christian-kramer/Overwatch-Reaper-Costume/Reference Images/384cf658570ae1bcbe017ebe22efb558.png

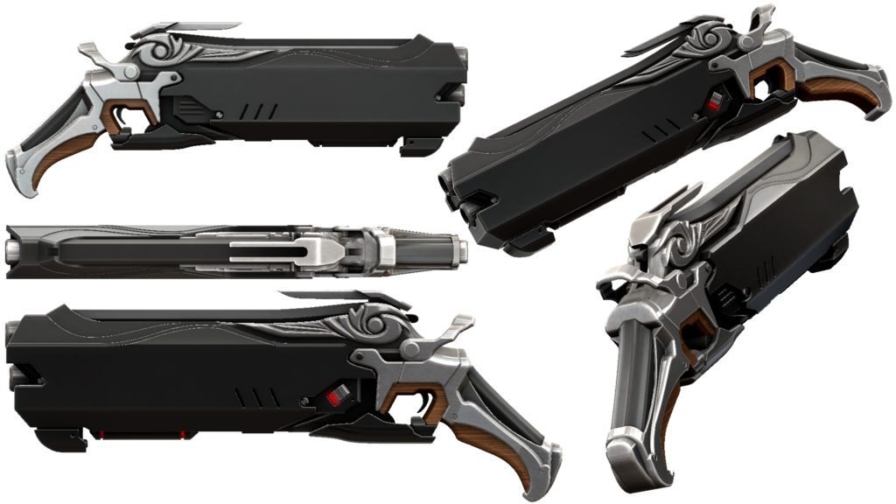
Reference Images/384cf658570ae1bcbe017ebe22efb558.png
