christian-kramer/Overwatch-Reaper-Costume/Reference Images/Reaper_Enigmatic.jpg

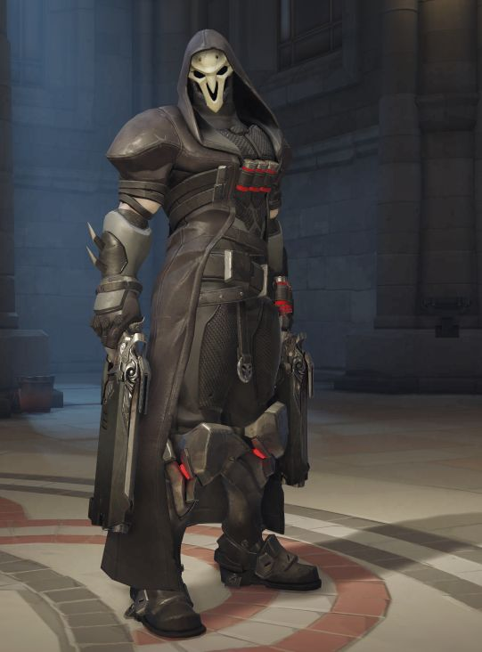
Reference Images/Reaper_Enigmatic.jpg
