christian-kramer/Overwatch-Reaper-Costume/Mechanical/Armor/To Print/Left Calf Cover Top Parts/Left Calf Cover Top Part 8.stl

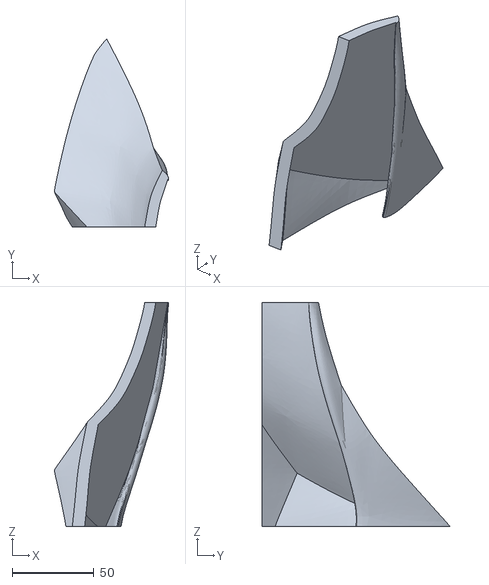
[picture p23: CAD file, 2019-10-07]
Mechanical/Armor/To Print/Left Calf Cover Top Parts/Left Calf Cover Top Part 8.stl
70.2 x 115.3 x 137.3
