christian-kramer/Overwatch-Reaper-Costume/Mechanical/Armor/To Print/Right Kneecap.stl

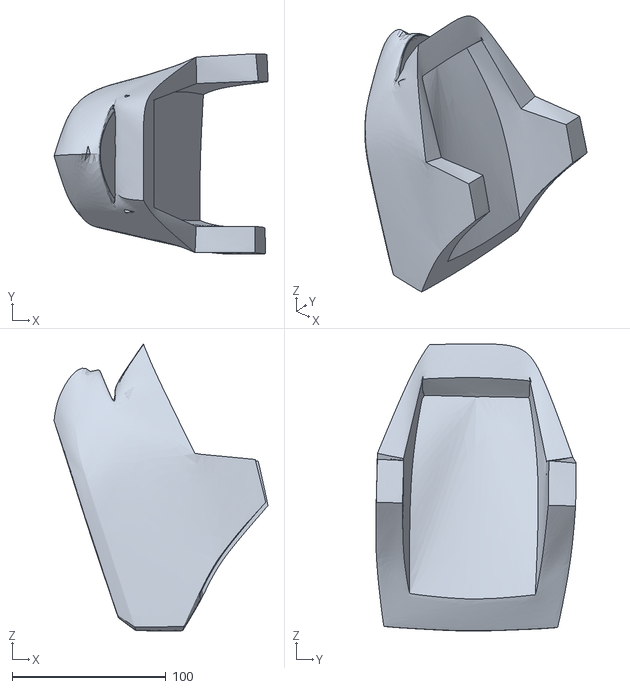
[picture p24: CAD file, 2019-10-07]
Mechanical/Armor/To Print/Right Kneecap.stl
139.2 x 130.5 x 186.8
