christian-kramer/Overwatch-Reaper-Costume/Mechanical/Details/2reaper-emblem.stl

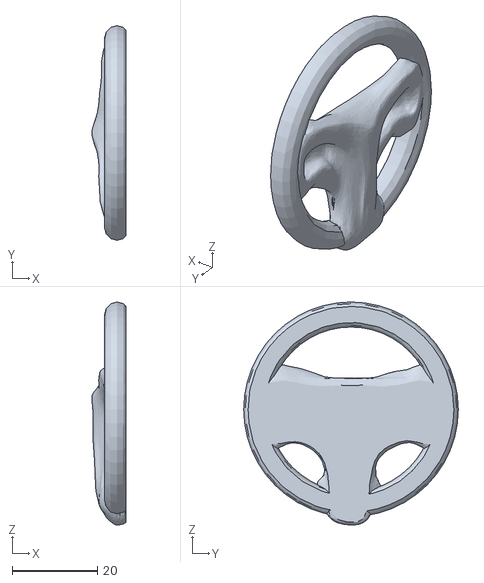
[picture p25: CAD file, 2019-08-23]
Mechanical/Details/2reaper-emblem.stl
8.07 x 50.5 x 52.4
