christian-kramer/Overwatch-Reaper-Costume/Mechanical/Details/To Print/Belt Case Lower Shell.stl

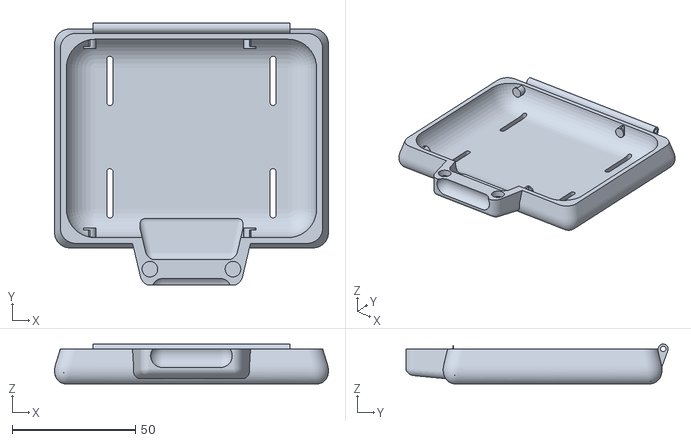
[picture p26: CAD file, 2019-08-24]
Mechanical/Details/To Print/Belt Case Lower Shell.stl
111.1 x 106.4 x 16.2
