christian-kramer/Overwatch-Reaper-Costume/Mechanical/Gun/Original/Hellfire-shot-guns-Brown-hellfire-handle-C.STL

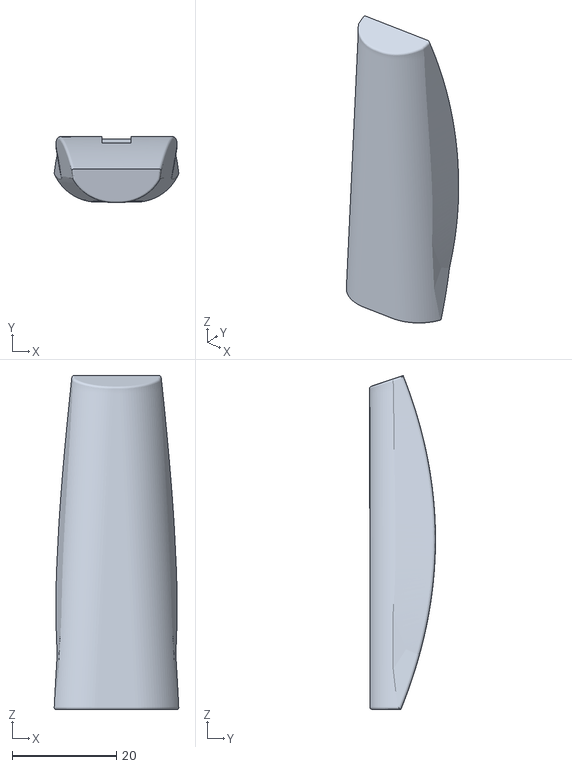
[picture p27: CAD file, 2019-04-04]
Mechanical/Gun/Original/Hellfire-shot-guns-Brown-hellfire-handle-C.STL
23.9 x 12.7 x 64.1
