christian-kramer/Overwatch-Reaper-Costume/Mechanical/Gun/Test/Right Hand Larger.stl

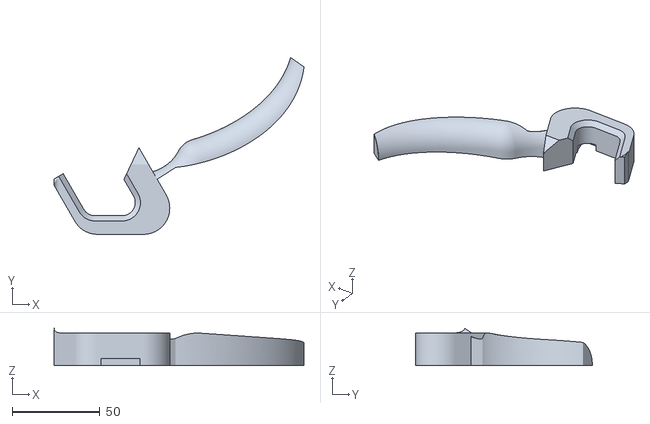
[picture p28: CAD file, 2019-04-12]
Mechanical/Gun/Test/Right Hand Larger.stl
142.7 x 100.9 x 21.3
