christian-kramer/Overwatch-Reaper-Costume/Mechanical/Gun/To Print/Butt.stl

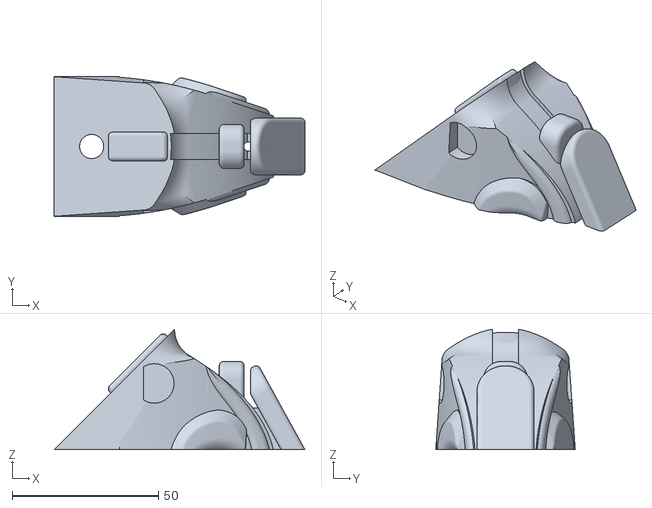
[picture p29: CAD file, 2019-10-12]
Mechanical/Gun/To Print/Butt.stl
85.8 x 47.7 x 41.1
