christian-kramer/Overwatch-Reaper-Costume/Mechanical/PCB Ship Container/To Print/Lid.stl

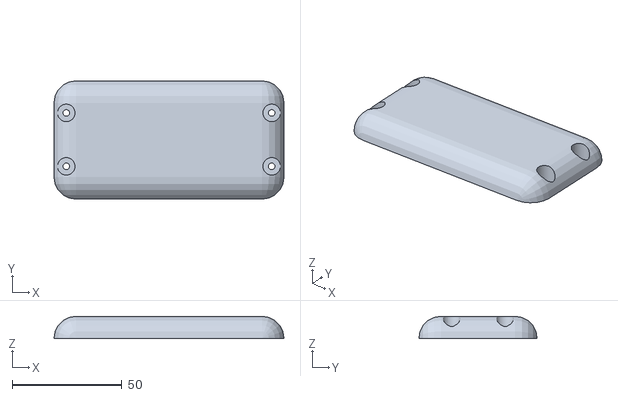
[picture p30: CAD file, 2019-08-11]
Mechanical/PCB Ship Container/To Print/Lid.stl
105.0 x 54.0 x 10.2
