christian-kramer/Overwatch-Reaper-Costume/Mechanical/Armor/To Print/Left Calf Cover Top Parts/Left Calf Cover Top Part 6.stl

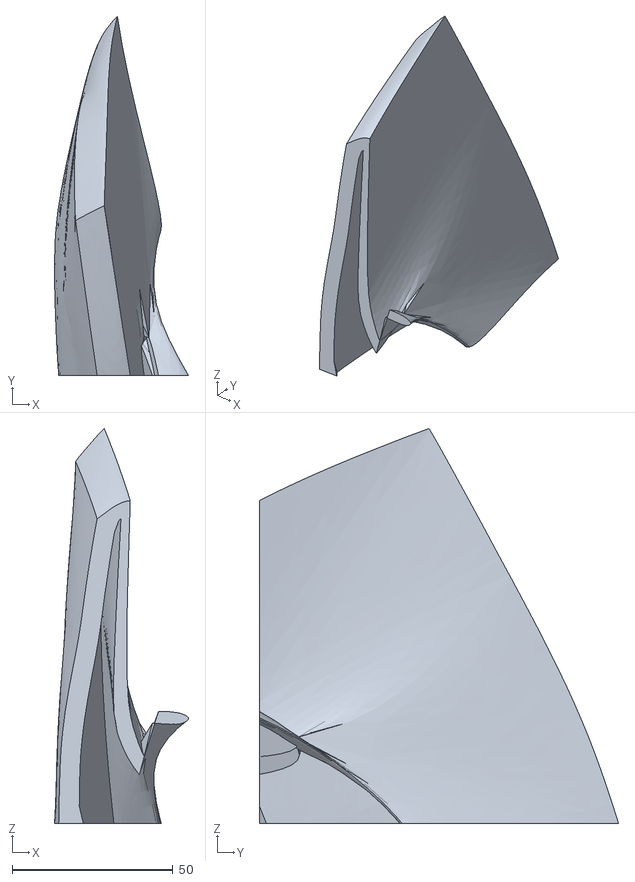
[picture p31: CAD file, 2019-10-07]
Mechanical/Armor/To Print/Left Calf Cover Top Parts/Left Calf Cover Top Part 6.stl
41.6 x 111.6 x 122.7
