christian-kramer/Overwatch-Reaper-Costume/Mechanical/Gun/Components/LED 5mm.STL

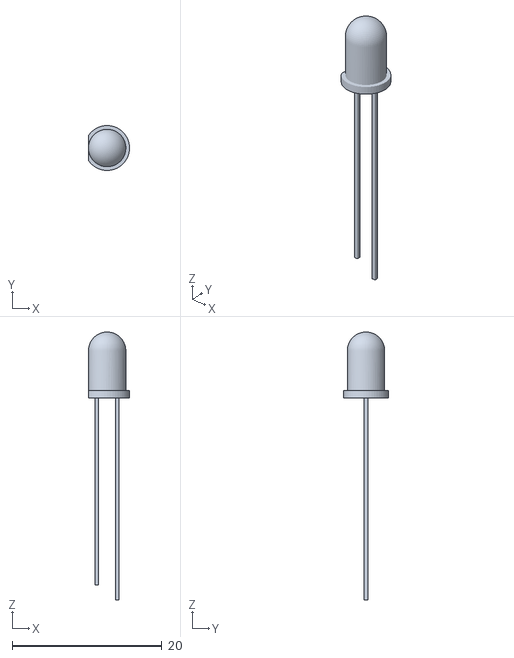
[picture p32: CAD file, 2019-04-12]
Mechanical/Gun/Components/LED 5mm.STL
5.50 x 6.00 x 35.8
