christian-kramer/Overwatch-Reaper-Costume/Mechanical/Gun/Test/Barrel B Top Fixed.stl

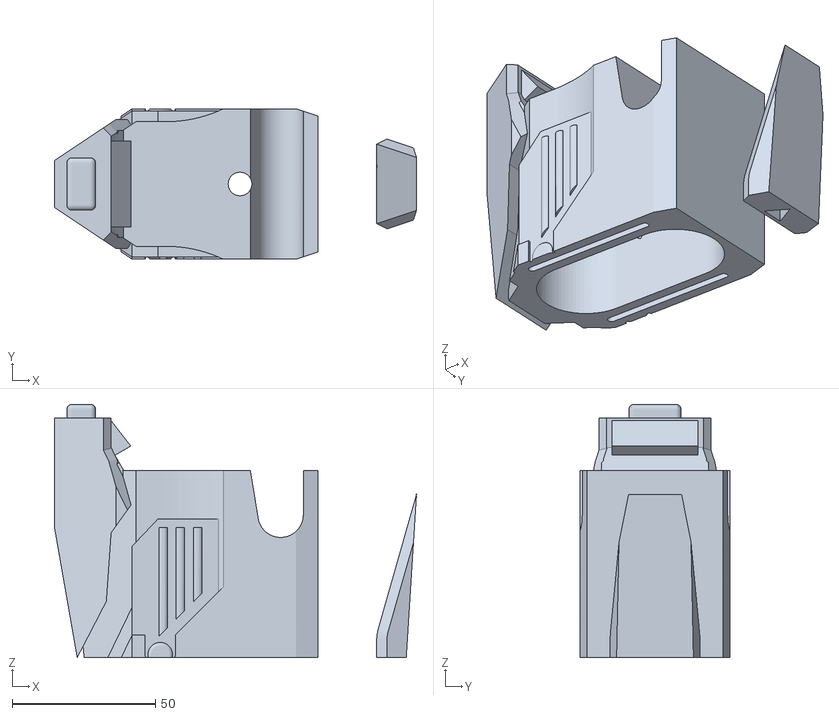
[picture p33: CAD file, 2019-04-12]
Mechanical/Gun/Test/Barrel B Top Fixed.stl
126.3 x 52.5 x 88.3
