christian-kramer/Overwatch-Reaper-Costume/Mechanical/Gun/To Print/Trigger Handles.stl

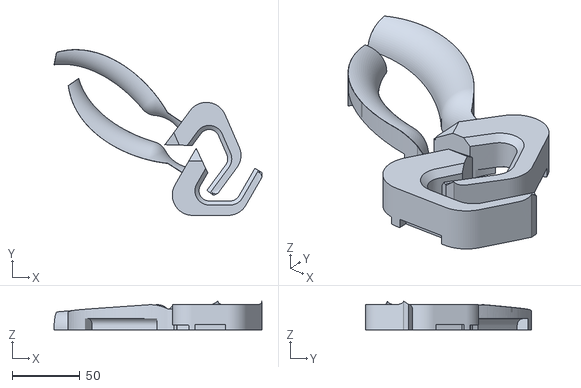
[picture p34: CAD file, 2019-10-12]
Mechanical/Gun/To Print/Trigger Handles.stl
153.2 x 122.1 x 21.2
