christian-kramer/Overwatch-Reaper-Costume/Mechanical/Armor/To Print/Left Calf Cover Bottom Half 1.stl

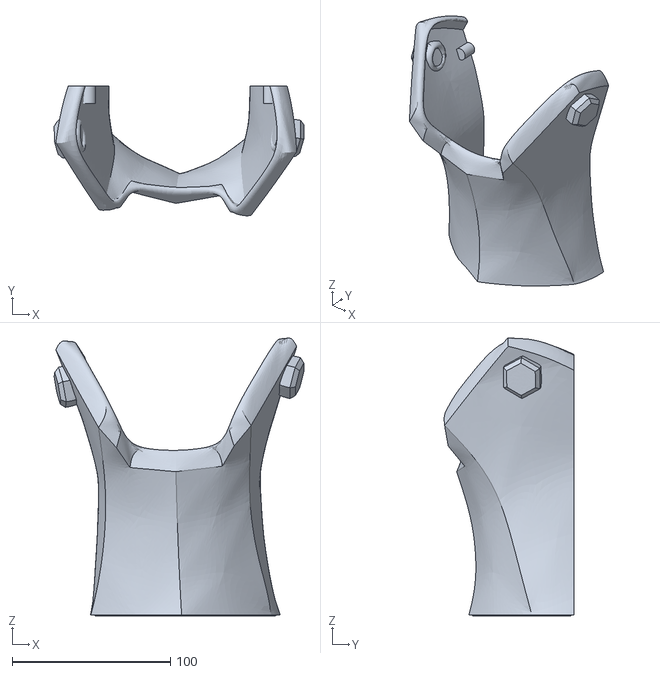
[picture p35: CAD file, 2019-09-20]
Mechanical/Armor/To Print/Left Calf Cover Bottom Half 1.stl
157.6 x 81.9 x 175.4
