christian-kramer/Overwatch-Reaper-Costume/Mechanical/Armor/To Print/Left Calf Cover Top Parts/Left Calf Cover Top Part 3.stl

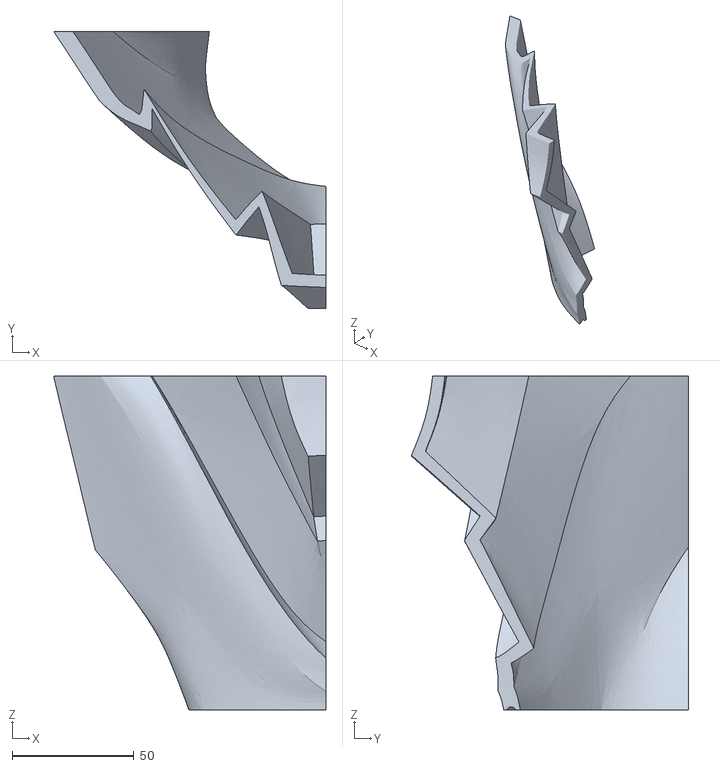
[picture p36: CAD file, 2019-10-07]
Mechanical/Armor/To Print/Left Calf Cover Top Parts/Left Calf Cover Top Part 3.stl
111.7 x 114.0 x 137.3
