christian-kramer/Overwatch-Reaper-Costume/Mechanical/Armor/To Print/Right Calf Cover Top Parts/Right Calf Cover Top Part 4.stl

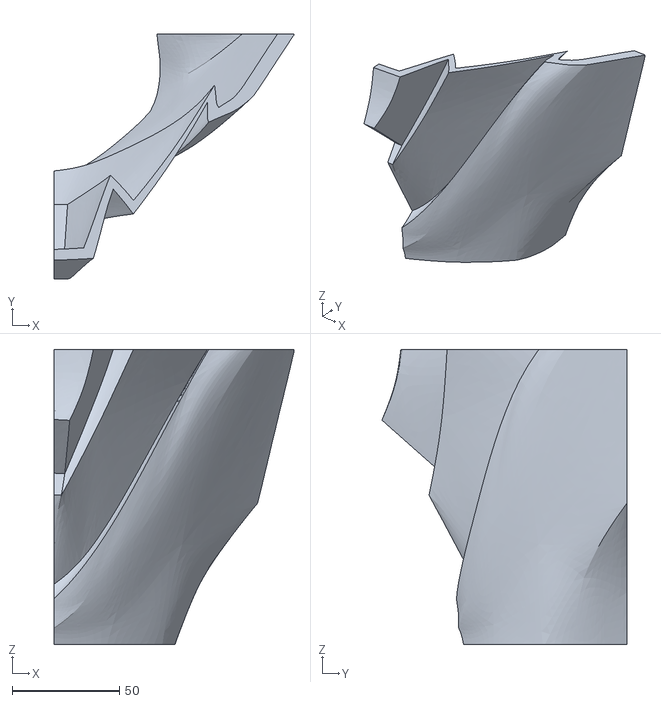
[picture p37: CAD file, 2019-10-07]
Mechanical/Armor/To Print/Right Calf Cover Top Parts/Right Calf Cover Top Part 4.stl
112.1 x 114.4 x 137.8
