christian-kramer/Overwatch-Reaper-Costume/Mechanical/Gun/Components/KEYSTONE 2460.step

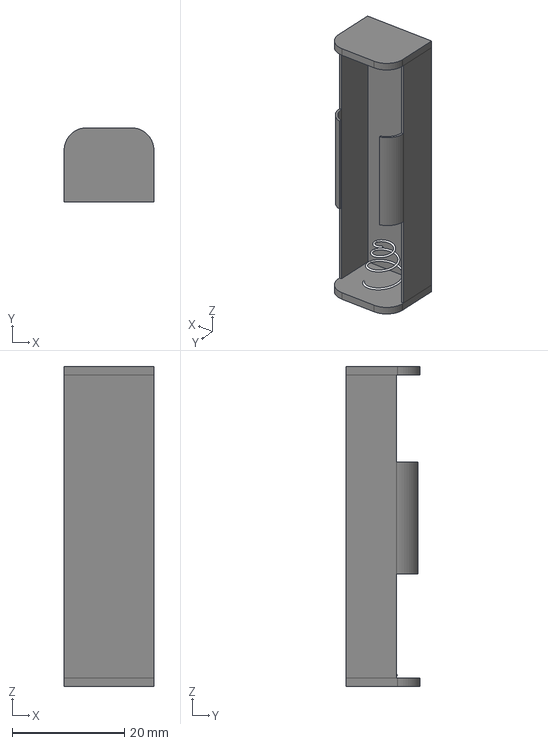
[picture p38: CAD file, 2019-04-12]
Mechanical/Gun/Components/KEYSTONE 2460.step
16.0 x 13.3 x 57.0 mm
