christian-kramer/Overwatch-Reaper-Costume/Mechanical/Gun/Original/Hellfire-shot-guns-Silver-PLA-hellfire-handle.STL

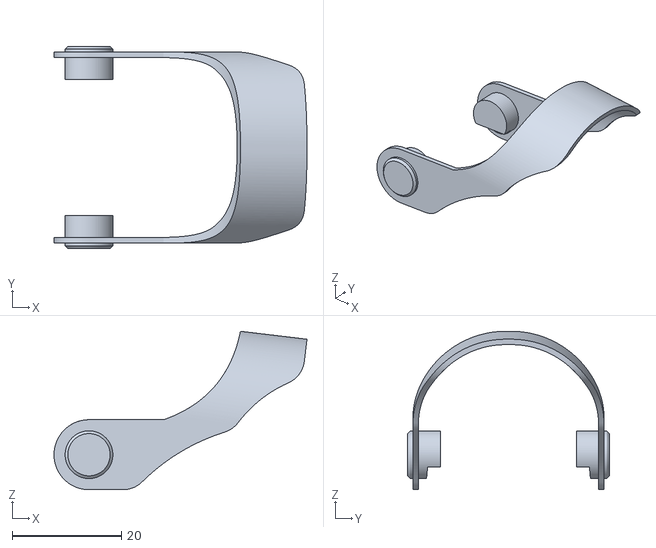
[picture p39: CAD file, 2019-04-04]
Mechanical/Gun/Original/Hellfire-shot-guns-Silver-PLA-hellfire-handle.STL
46.4 x 37.0 x 29.0
