christian-kramer/Overwatch-Reaper-Costume/Mechanical/Gun/Test/Barrel B3.stl

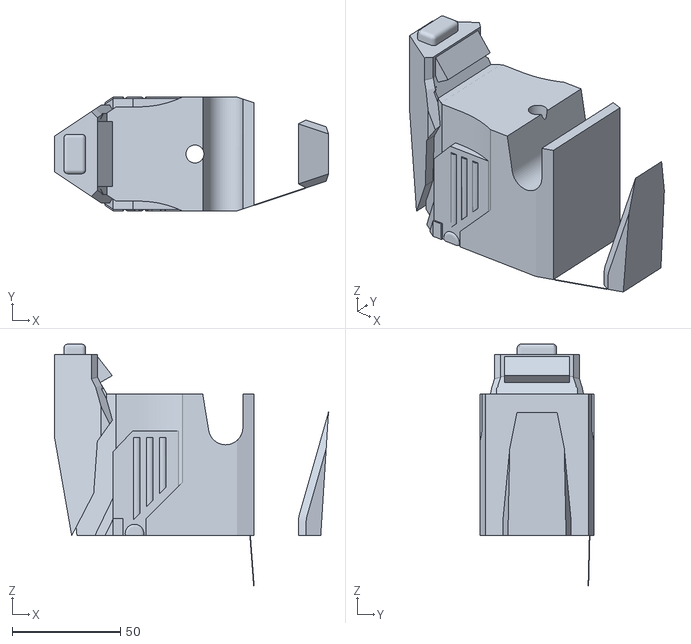
[picture p40: CAD file, 2019-04-12]
Mechanical/Gun/Test/Barrel B3.stl
126.3 x 52.5 x 111.5
