christian-kramer/Overwatch-Reaper-Costume/Mechanical/Gun/To Print/Barrel A Shell 1.stl

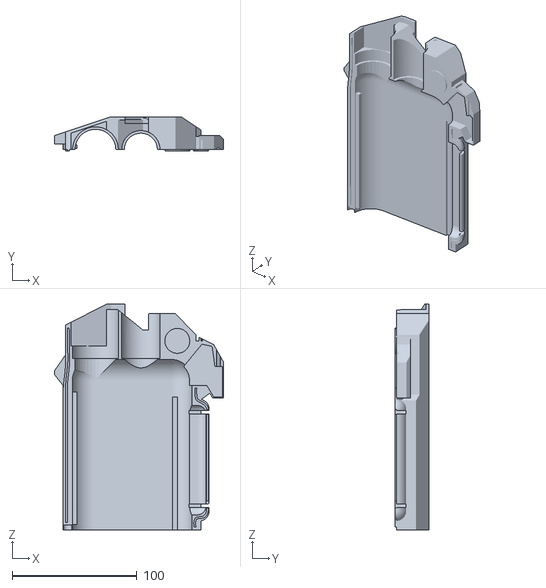
[picture p41: CAD file, 2019-10-12]
Mechanical/Gun/To Print/Barrel A Shell 1.stl
135.9 x 27.3 x 181.5
