christian-kramer/Overwatch-Reaper-Costume/Mechanical/Armor/To Print/Left Calf Cover Top Parts/Left Calf Cover Top Part 5.stl

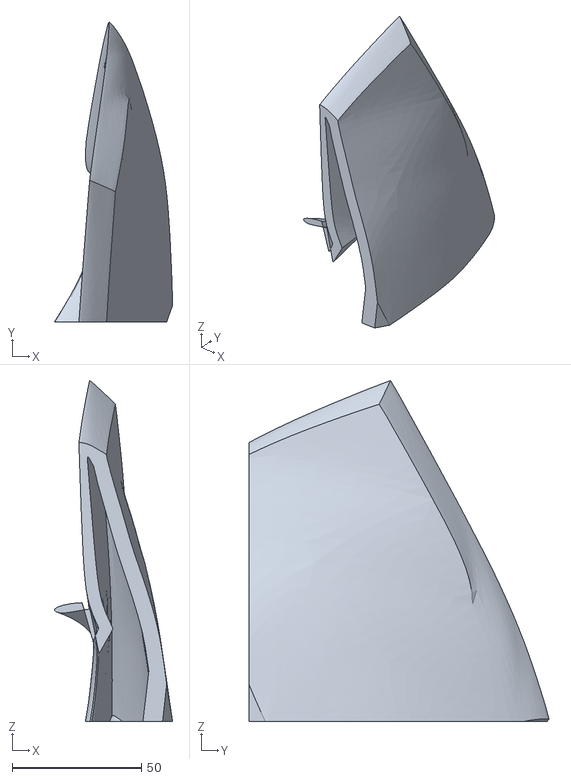
[picture p42: CAD file, 2019-10-07]
Mechanical/Armor/To Print/Left Calf Cover Top Parts/Left Calf Cover Top Part 5.stl
45.7 x 116.1 x 131.9
