christian-kramer/Overwatch-Reaper-Costume/Mechanical/Armor/To Print/Right Calf Cover Top Parts/Right Calf Cover Top Part 3.stl

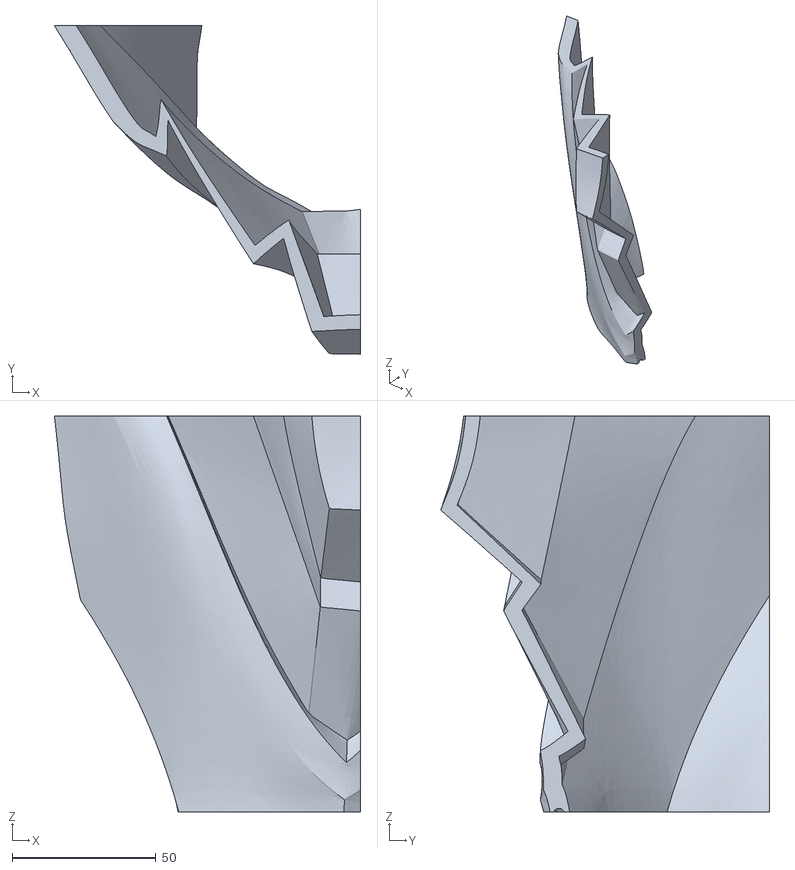
[picture p43: CAD file, 2019-10-07]
Mechanical/Armor/To Print/Right Calf Cover Top Parts/Right Calf Cover Top Part 3.stl
106.5 x 114.3 x 137.8
