christian-kramer/Overwatch-Reaper-Costume/Mechanical/Gun/Original/Hellfire-shot-guns-Silver-PLA-hellfire-barrel.STL

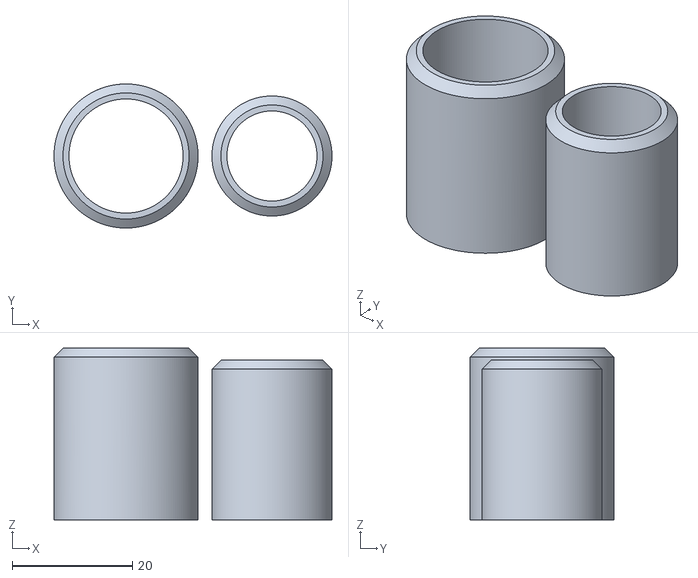
[picture p44: CAD file, 2019-04-04]
Mechanical/Gun/Original/Hellfire-shot-guns-Silver-PLA-hellfire-barrel.STL
46.3 x 24.0 x 28.6
