christian-kramer/Overwatch-Reaper-Costume/Mechanical/Gun/Test/Barrel B Bottom.stl

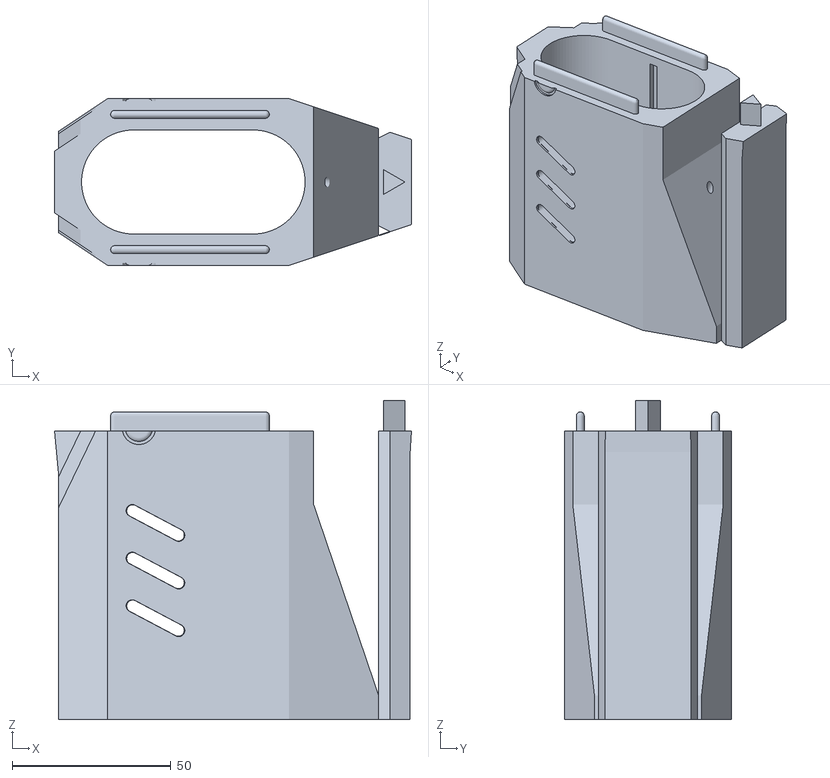
[picture p45: CAD file, 2019-04-12]
Mechanical/Gun/Test/Barrel B Bottom.stl
112.4 x 52.5 x 100.5
