christian-kramer/Overwatch-Reaper-Costume/Mechanical/Gun/To Print/Barrel B Bottom.stl

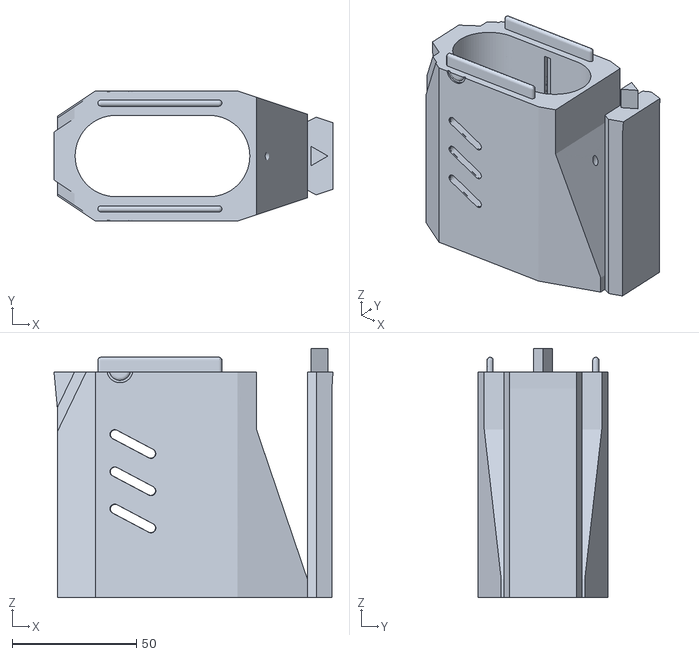
[picture p46: CAD file, 2019-10-12]
Mechanical/Gun/To Print/Barrel B Bottom.stl
112.4 x 52.5 x 100.5
