christian-kramer/Overwatch-Reaper-Costume/Mechanical/Armor/To Print/Left Calf Cover Bottom Half 2.stl

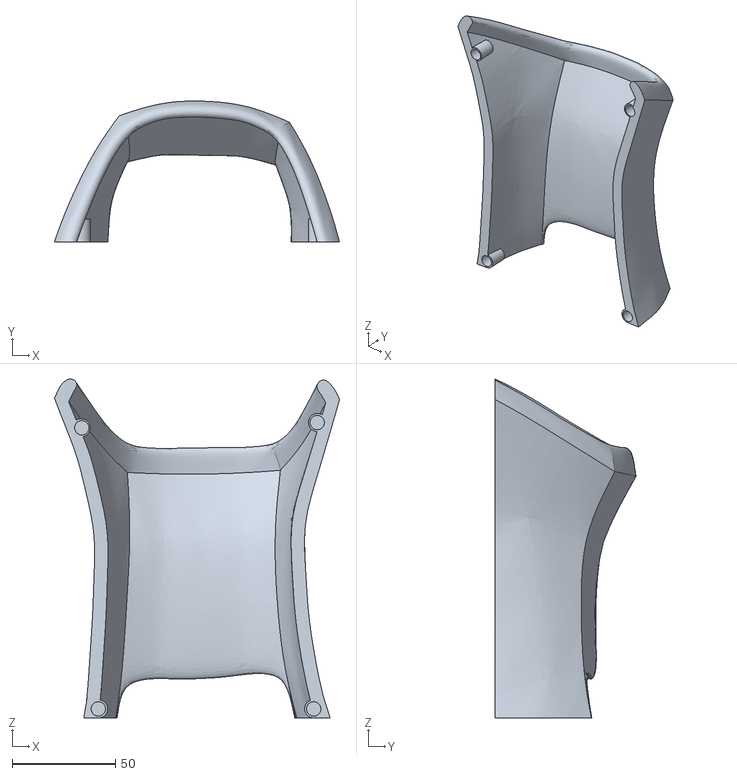
[picture p47: CAD file, 2019-09-20]
Mechanical/Armor/To Print/Left Calf Cover Bottom Half 2.stl
138.2 x 68.3 x 164.4
