christian-kramer/Overwatch-Reaper-Costume/Mechanical/Armor/To Print/Left Calf Cover Top Parts/Left Calf Cover Top Part 2.stl

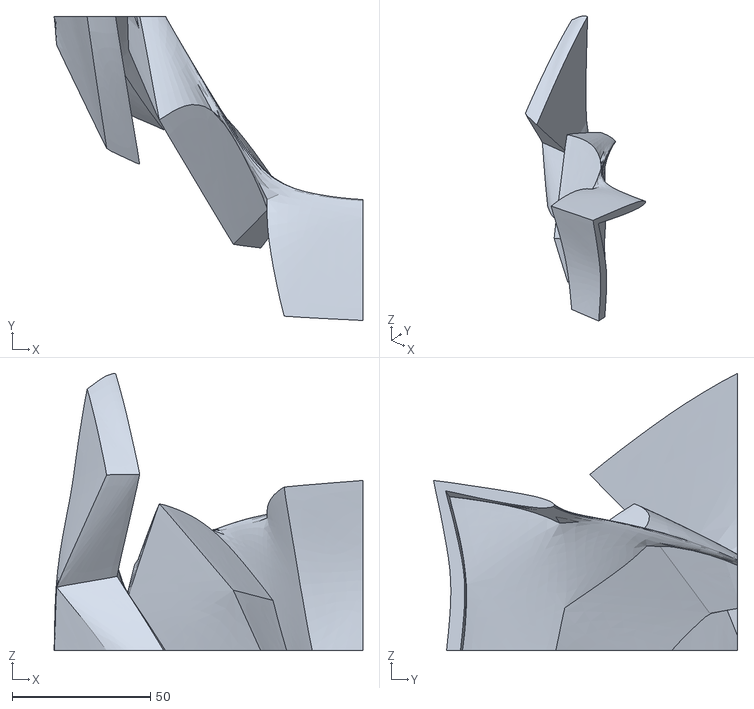
[picture p48: CAD file, 2019-10-07]
Mechanical/Armor/To Print/Left Calf Cover Top Parts/Left Calf Cover Top Part 2.stl
111.7 x 110.0 x 100.3
