christian-kramer/Overwatch-Reaper-Costume/Mechanical/Gun/Test/Barrel B Top.stl

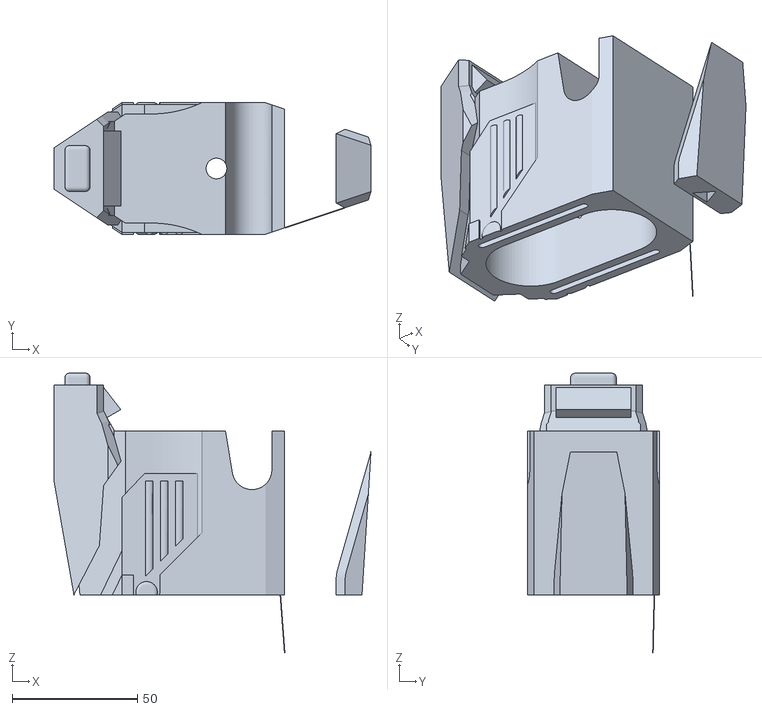
[picture p49: CAD file, 2019-04-12]
Mechanical/Gun/Test/Barrel B Top.stl
126.3 x 52.5 x 111.5
