christian-kramer/Overwatch-Reaper-Costume/Mechanical/Gun/To Print/Trigger Handle Left.stl

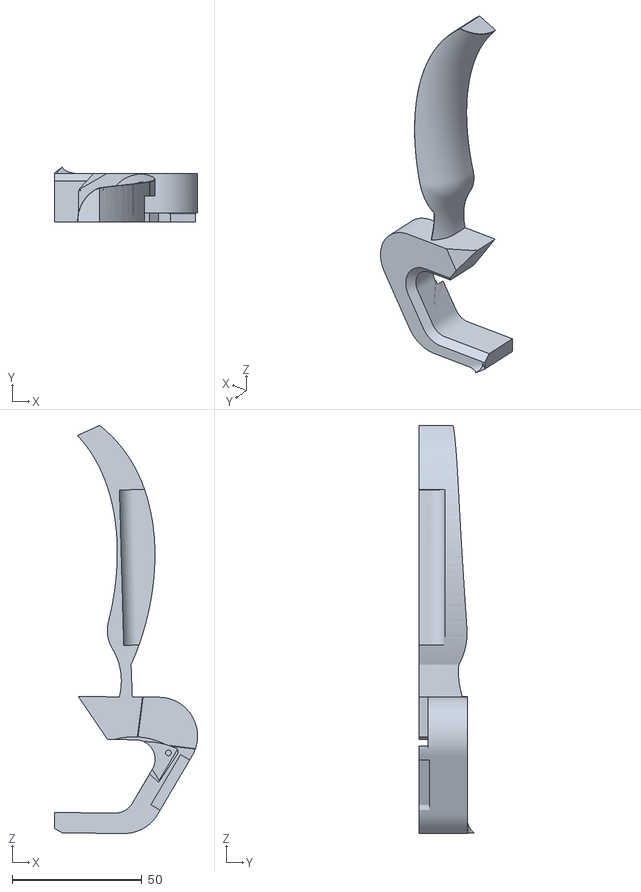
[picture p50: CAD file, 2019-09-25]
Mechanical/Gun/To Print/Trigger Handle Left.stl
55.3 x 21.3 x 157.5
