christian-kramer/Overwatch-Reaper-Costume/Mechanical/Armor/To Print/Right Calf Cover Top Parts/Right Calf Cover Top Part 2.stl

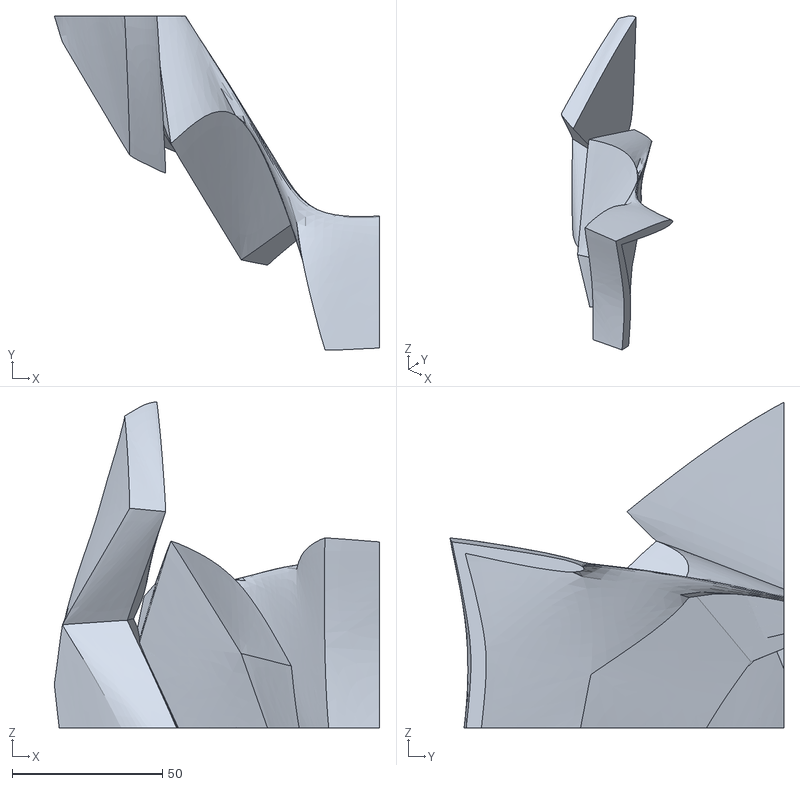
[picture p51: CAD file, 2019-10-07]
Mechanical/Armor/To Print/Right Calf Cover Top Parts/Right Calf Cover Top Part 2.stl
108.2 x 111.0 x 108.2
