christian-kramer/Overwatch-Reaper-Costume/Mechanical/Gun/Original/Hellfire-shot-guns-Silver-PLA-hellfire-back-body-b.STL

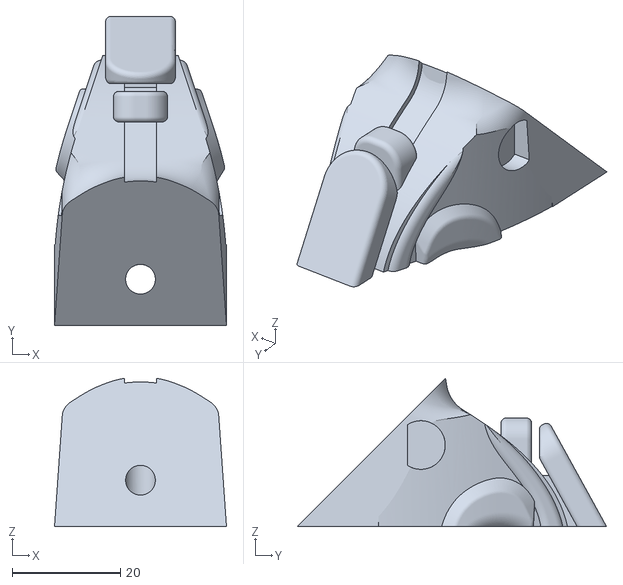
[picture p52: CAD file, 2019-04-04]
Mechanical/Gun/Original/Hellfire-shot-guns-Silver-PLA-hellfire-back-body-b.STL
31.8 x 57.2 x 27.4
