christian-kramer/Overwatch-Reaper-Costume/Mechanical/Gun/Test/hollow.stl

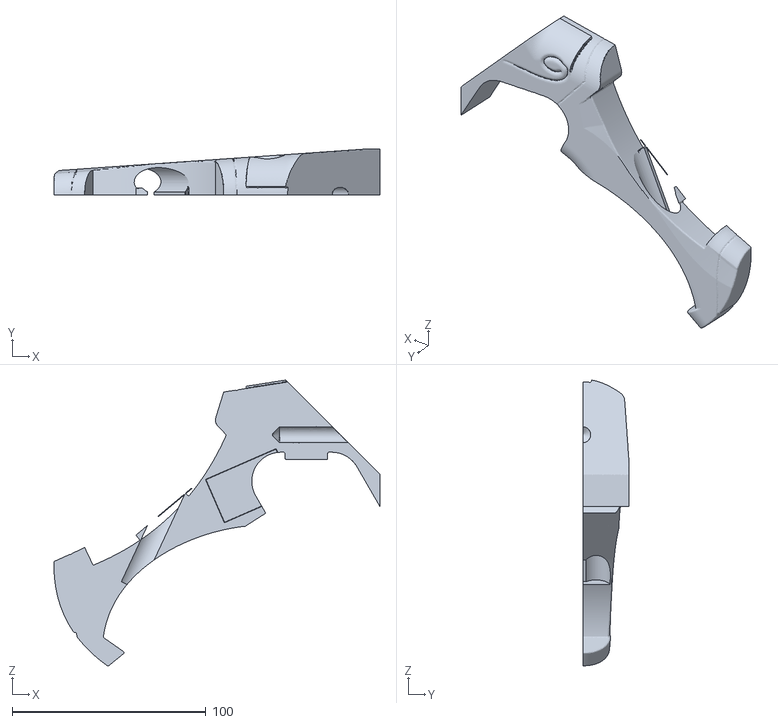
[picture p53: CAD file, 2019-04-12]
Mechanical/Gun/Test/hollow.stl
168.3 x 24.0 x 147.5
