christian-kramer/Overwatch-Reaper-Costume/Mechanical/Armor/To Print/Left Calf Cover Top.stl

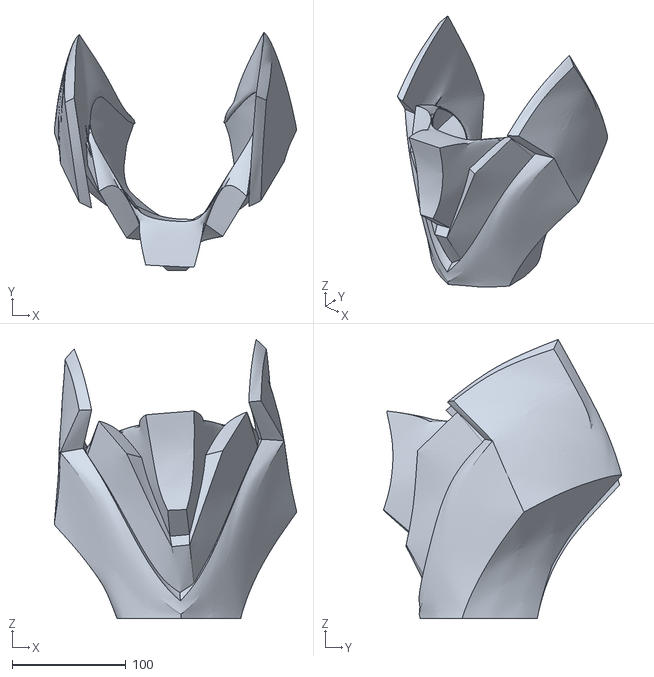
[picture p54: CAD file, 2019-09-18]
Mechanical/Armor/To Print/Left Calf Cover Top.stl
213.0 x 209.4 x 245.0
