christian-kramer/Overwatch-Reaper-Costume/Mechanical/Gun/Original/Hellfire-shot-guns-Black-PLA-hellfire-trigger.STL

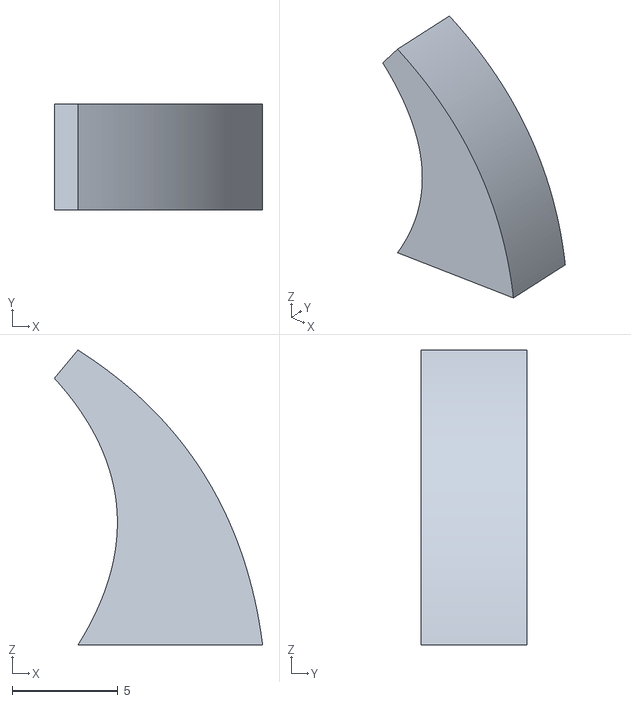
[picture p55: CAD file, 2019-04-04]
Mechanical/Gun/Original/Hellfire-shot-guns-Black-PLA-hellfire-trigger.STL
9.85 x 5.00 x 13.9
