christian-kramer/Overwatch-Reaper-Costume/Mechanical/Gun/To Print/Speaker Tray.stl

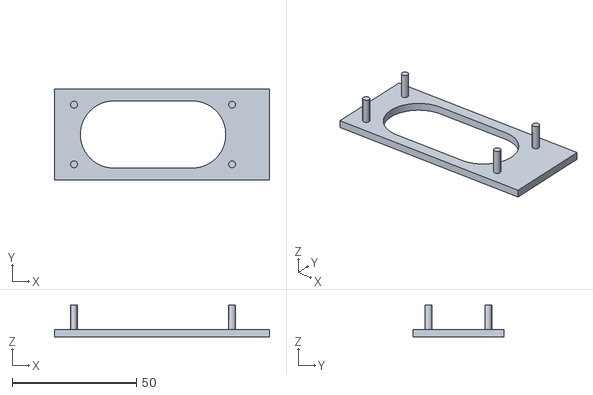
[picture p56: CAD file, 2019-09-24]
Mechanical/Gun/To Print/Speaker Tray.stl
86.5 x 36.7 x 12.7
