christian-kramer/Overwatch-Reaper-Costume/Mechanical/Armor/To Print/Boot Heel Decoration.stl

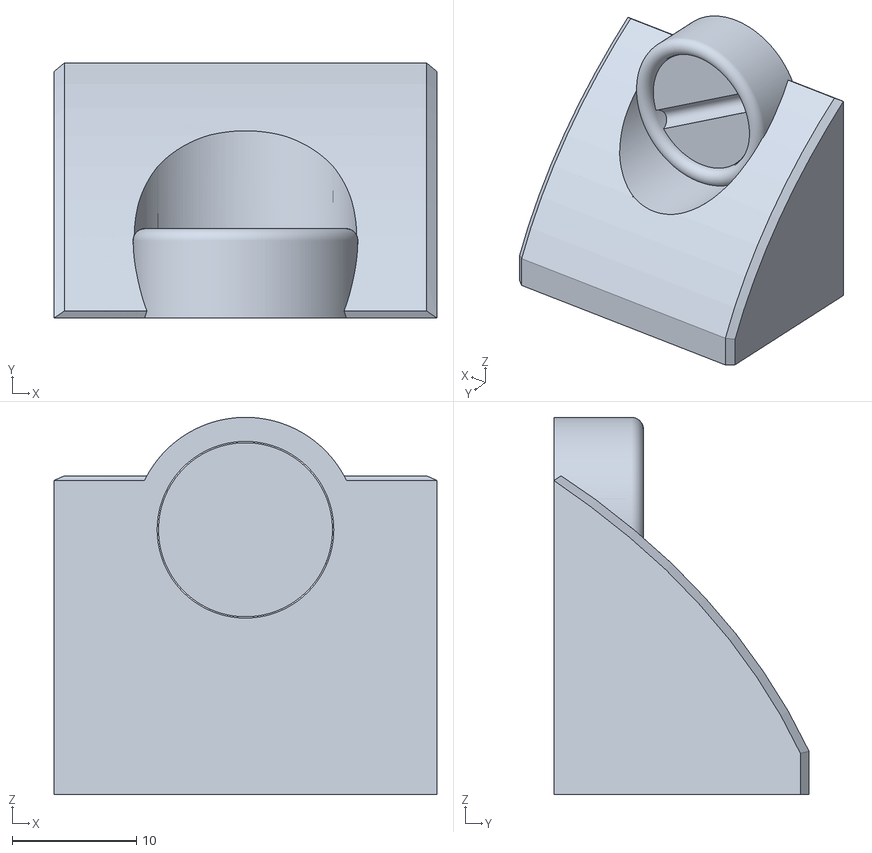
[picture p57: CAD file, 2019-09-12]
Mechanical/Armor/To Print/Boot Heel Decoration.stl
30.9 x 20.6 x 30.4
