christian-kramer/Overwatch-Reaper-Costume/Mechanical/Armor/To Print/Left Hand Spike.stl

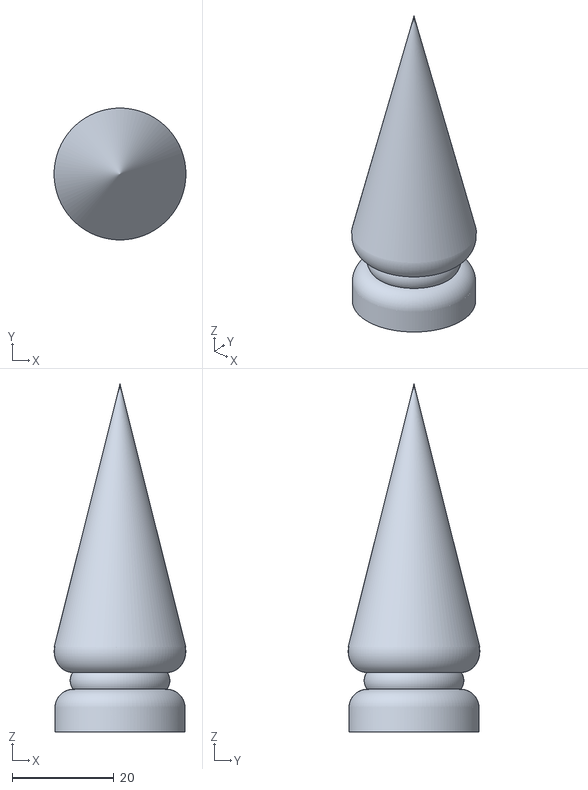
[picture p58: CAD file, 2019-09-12]
Mechanical/Armor/To Print/Left Hand Spike.stl
25.9 x 25.9 x 68.4
