christian-kramer/Overwatch-Reaper-Costume/Mechanical/Gun/To Print/Trigger-Thin.stl

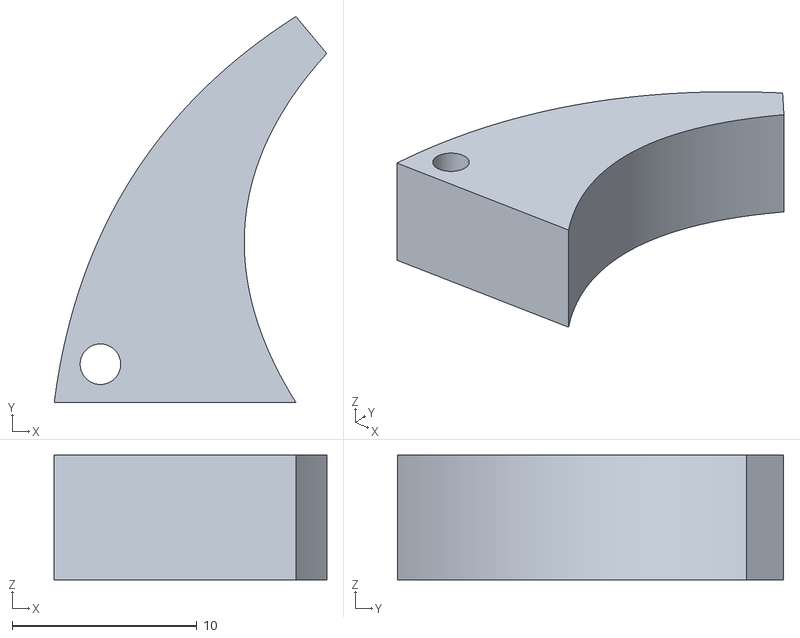
[picture p59: CAD file, 2019-09-24]
Mechanical/Gun/To Print/Trigger-Thin.stl
14.8 x 20.9 x 6.75
