christian-kramer/Overwatch-Reaper-Costume/Mechanical/Armor/To Print/Left Boot Backing.stl

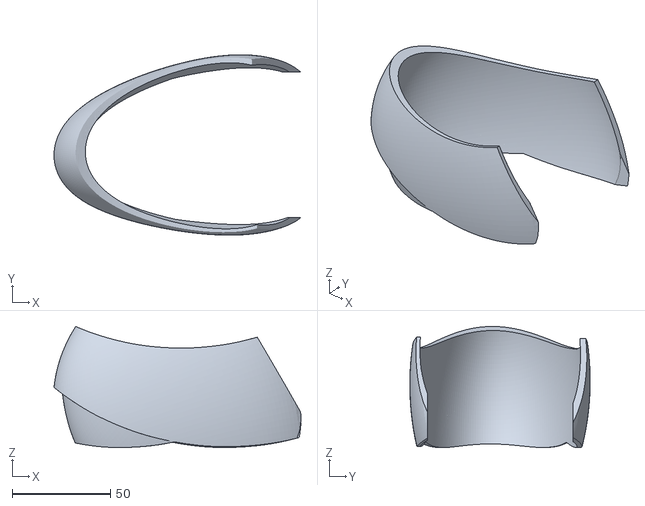
[picture p60: CAD file, 2019-09-11]
Mechanical/Armor/To Print/Left Boot Backing.stl
125.9 x 91.9 x 61.7
