christian-kramer/Overwatch-Reaper-Costume/Mechanical/Gun/To Print/Battery Cover (Wider Cavity).stl

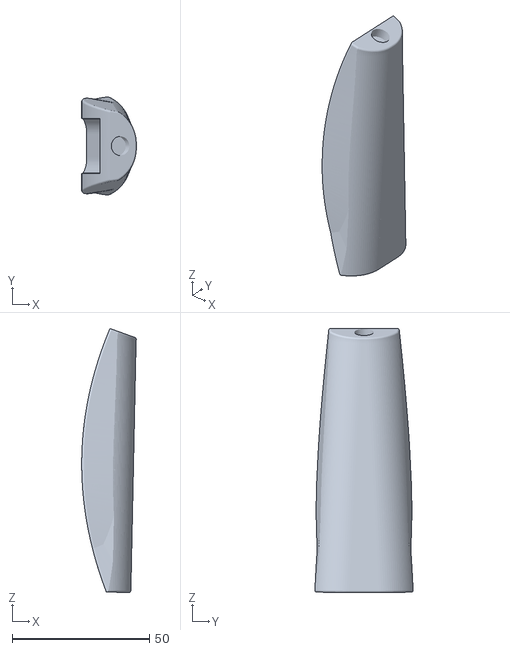
[picture p61: CAD file, 2019-09-24]
Mechanical/Gun/To Print/Battery Cover (Wider Cavity).stl
19.9 x 35.9 x 96.3
