christian-kramer/Overwatch-Reaper-Costume/Mechanical/Armor/To Print/Right Boot Cover.stl

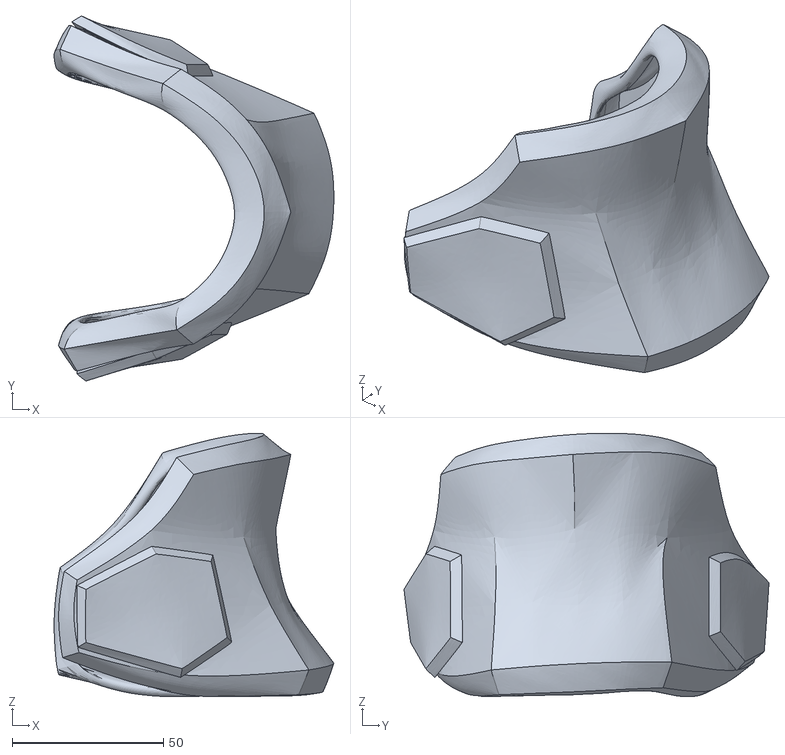
[picture p62: CAD file, 2019-09-11]
Mechanical/Armor/To Print/Right Boot Cover.stl
92.4 x 120.5 x 87.0
