christian-kramer/Overwatch-Reaper-Costume/Mechanical/Gun/To Print/Decorative Barrels.stl

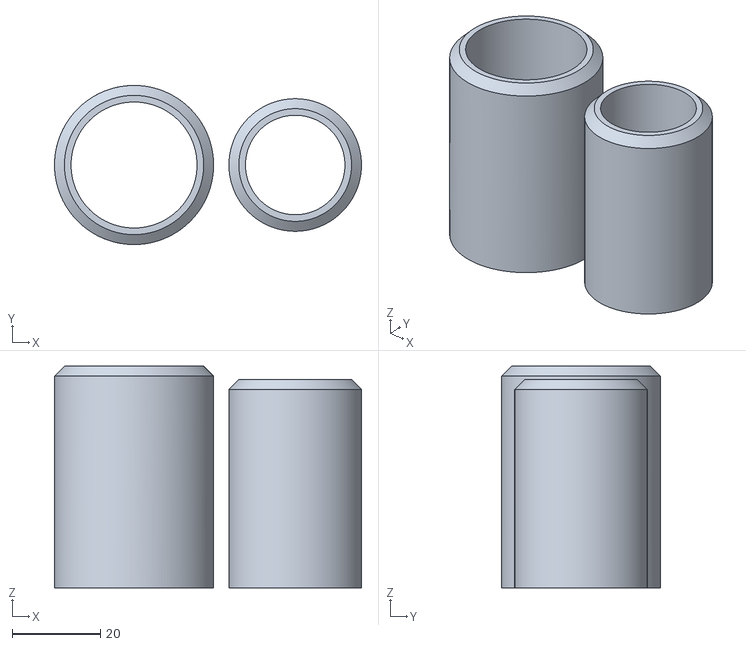
[picture p63: CAD file, 2019-09-14]
Mechanical/Gun/To Print/Decorative Barrels.stl
69.5 x 36.0 x 50.2
