christian-kramer/Overwatch-Reaper-Costume/Mechanical/Armor/To Print/Left Boot Heel.stl

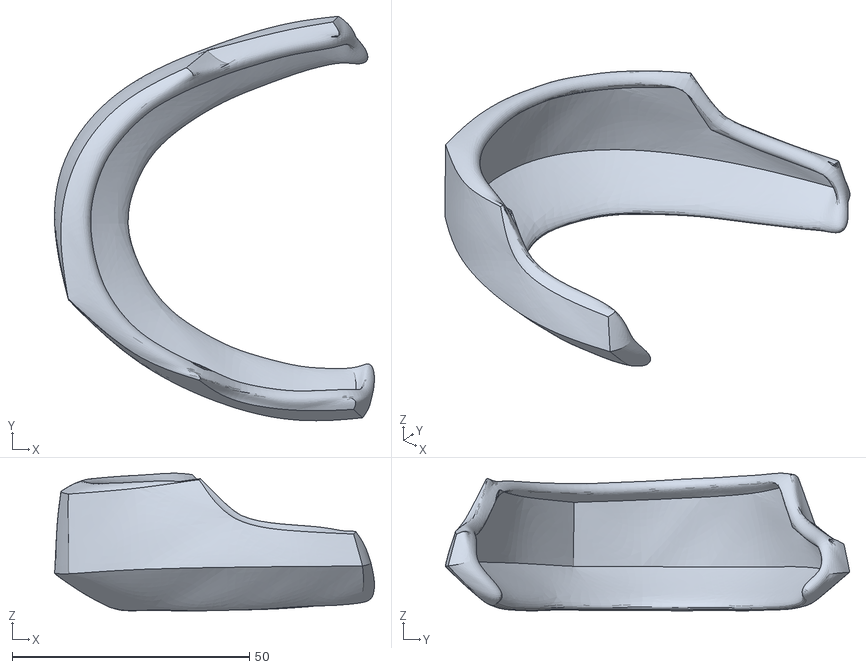
[picture p64: CAD file, 2019-09-11]
Mechanical/Armor/To Print/Left Boot Heel.stl
67.4 x 85.2 x 29.0
