christian-kramer/Overwatch-Reaper-Costume/Mechanical/Gun/To Print/Barrel B Top Decoration.stl

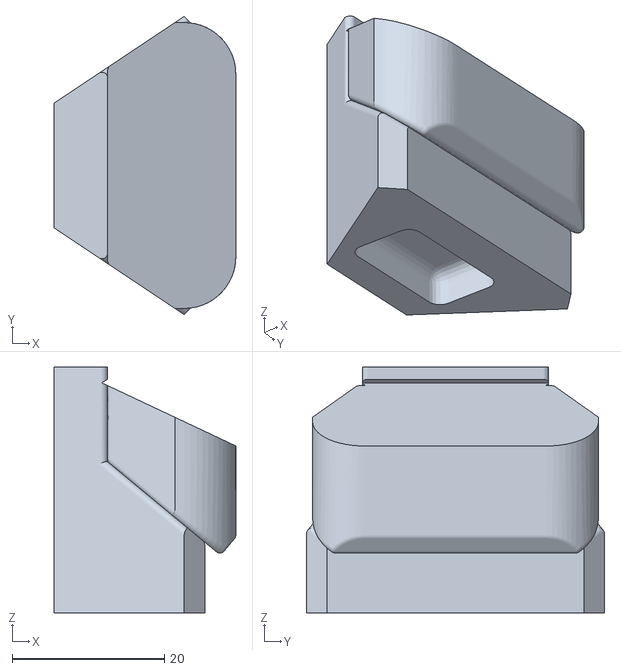
[picture p65: CAD file, 2019-08-12]
Mechanical/Gun/To Print/Barrel B Top Decoration.stl
23.8 x 39.1 x 32.3
