christian-kramer/Overwatch-Reaper-Costume/Mechanical/Gun/To Print/Trigger.stl

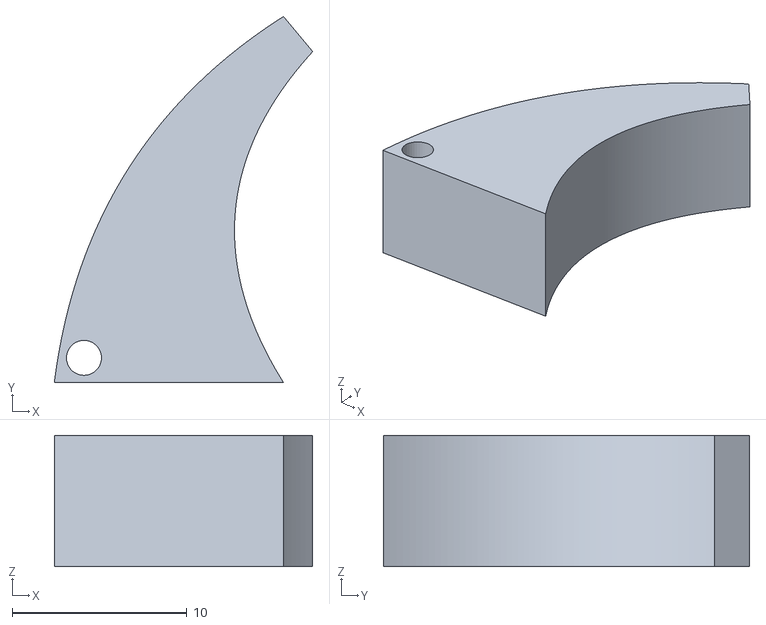
[picture p66: CAD file, 2019-07-21]
Mechanical/Gun/To Print/Trigger.stl
14.8 x 20.9 x 7.50
