christian-kramer/Overwatch-Reaper-Costume/Mechanical/Armor/To Print/Right Hand Cover.stl

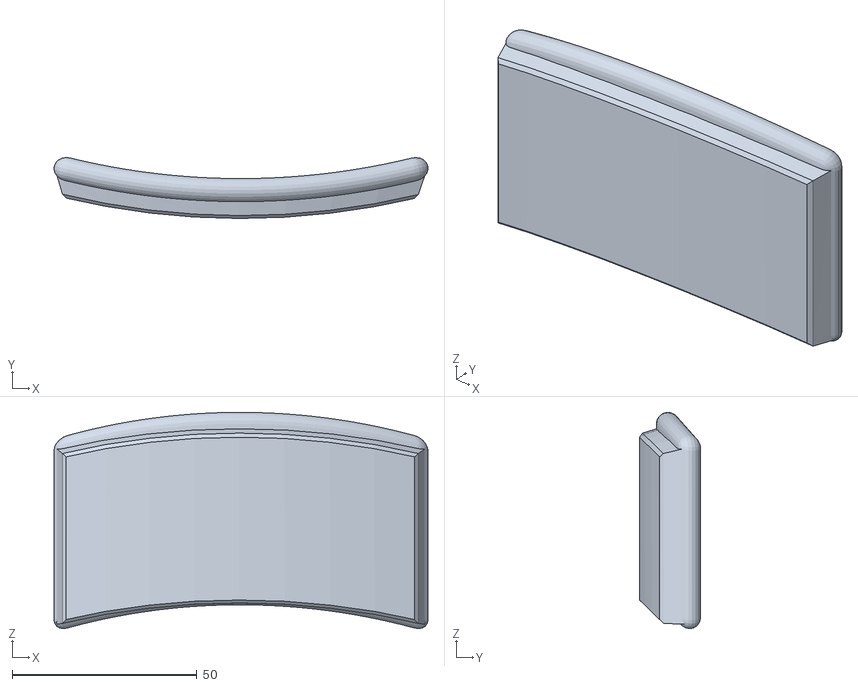
[picture p67: CAD file, 2019-09-05]
Mechanical/Armor/To Print/Right Hand Cover.stl
101.2 x 16.5 x 58.5
