christian-kramer/Overwatch-Reaper-Costume/Mechanical/Gun/To Print/Small Parts.stl

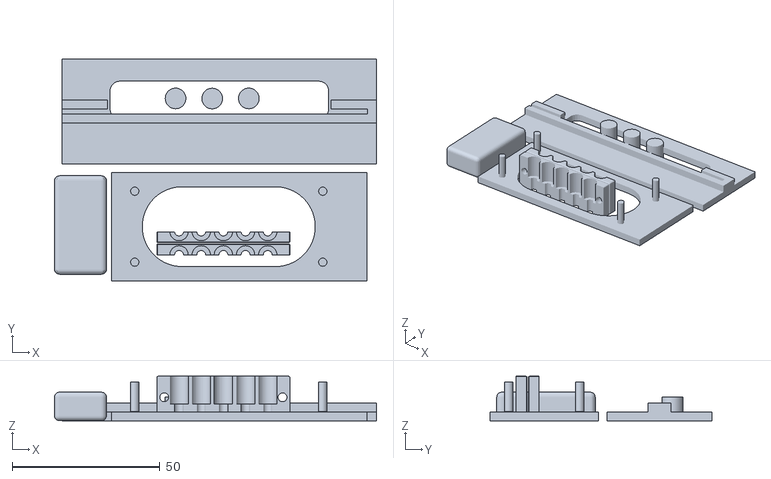
[picture p68: CAD file, 2019-06-20]
Mechanical/Gun/To Print/Small Parts.stl
108.9 x 75.0 x 15.1
