christian-kramer/Overwatch-Reaper-Costume/Mechanical/Armor/To Print/Left Gauntlet Bottom.stl

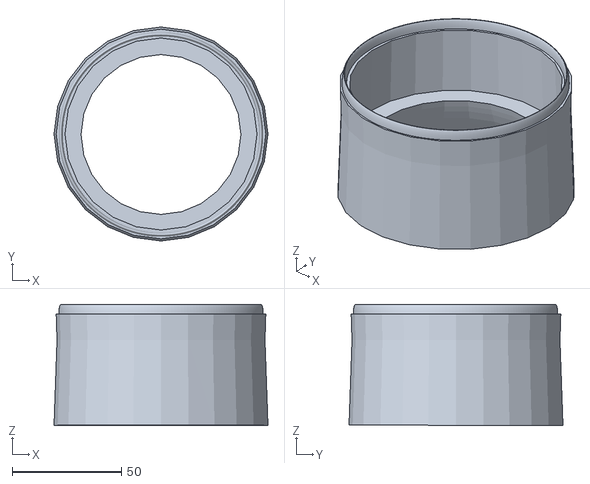
[picture p69: CAD file, 2019-09-04]
Mechanical/Armor/To Print/Left Gauntlet Bottom.stl
98.0 x 98.0 x 55.4
