christian-kramer/Overwatch-Reaper-Costume/Mechanical/Gun/To Print/Decorative Handle.stl

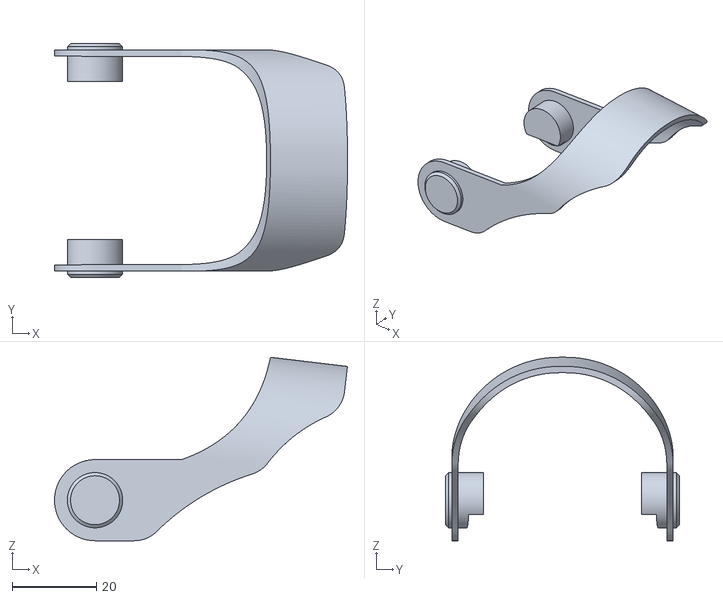
[picture p70: CAD file, 2019-04-12]
Mechanical/Gun/To Print/Decorative Handle.stl
69.5 x 55.5 x 43.5
