christian-kramer/Overwatch-Reaper-Costume/Mechanical/Armor/To Print/Right Gauntlet Shield.stl

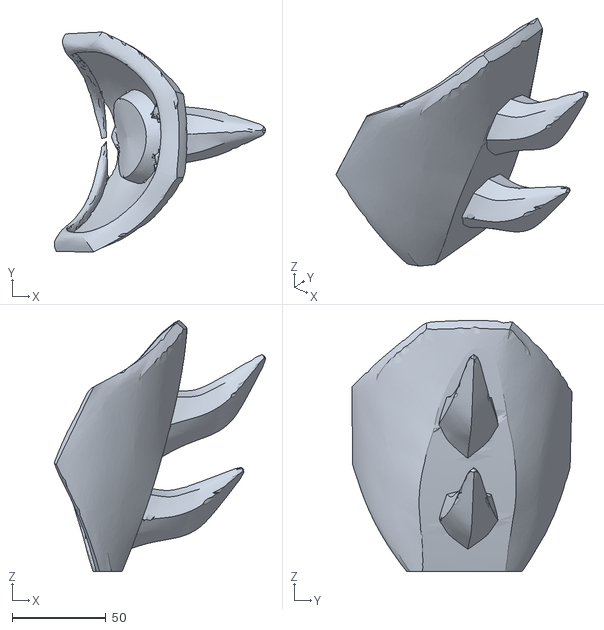
[picture p71: CAD file, 2019-09-04]
Mechanical/Armor/To Print/Right Gauntlet Shield.stl
112.8 x 117.3 x 134.0
