christian-kramer/Overwatch-Reaper-Costume/Mechanical/Gun/To Print/Battery Cover.stl

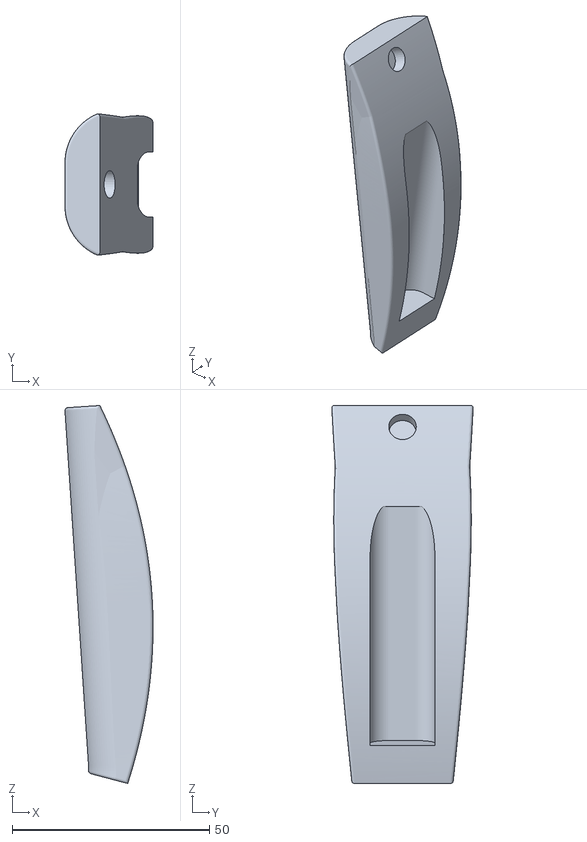
[picture p72: CAD file, 2019-04-12]
Mechanical/Gun/To Print/Battery Cover.stl
22.4 x 35.9 x 95.9
