christian-kramer/Overwatch-Reaper-Costume/Mechanical/Armor/To Print/Right Gauntlet Bottom.stl

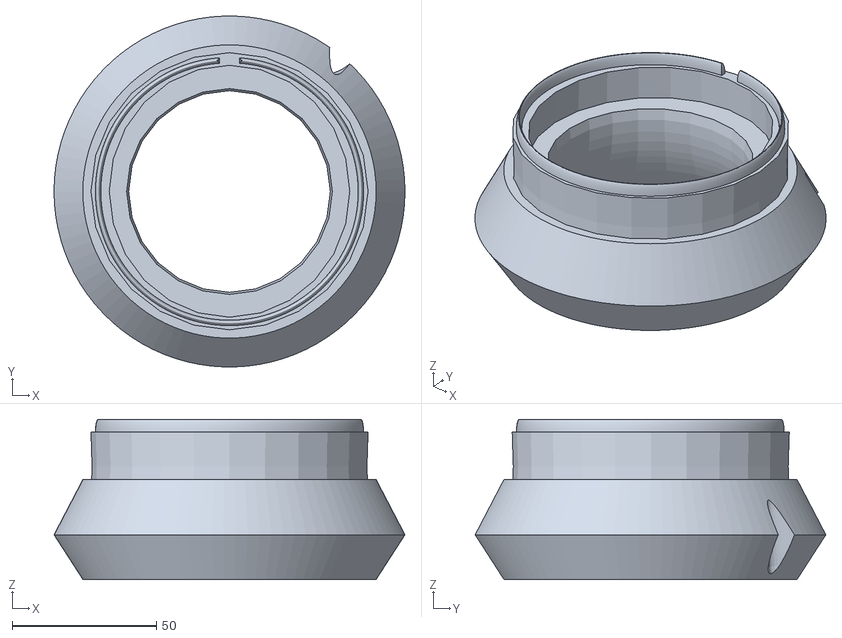
[picture p73: CAD file, 2019-09-04]
Mechanical/Armor/To Print/Right Gauntlet Bottom.stl
121.6 x 121.5 x 55.4
