christian-kramer/Overwatch-Reaper-Costume/Mechanical/Armor/To Print/Right Gauntlet Shield Clean.stl

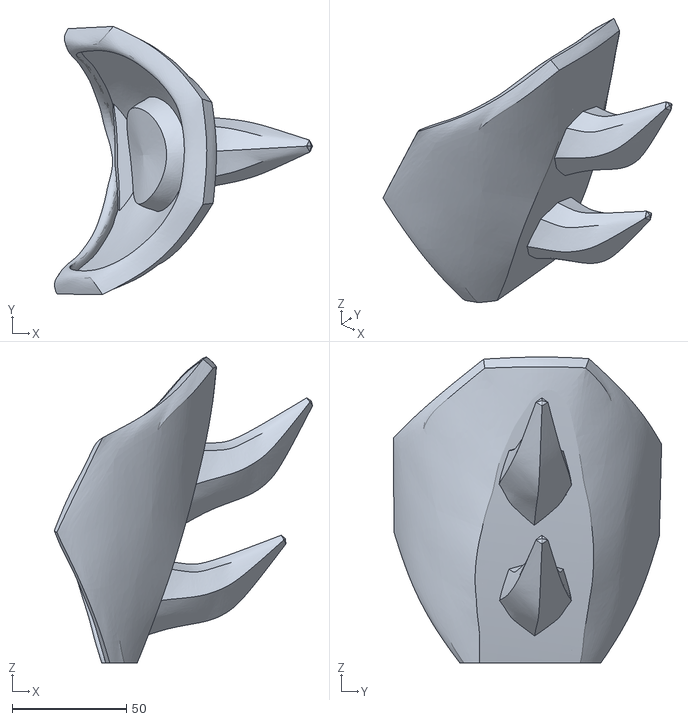
[picture p74: CAD file, 2019-09-04]
Mechanical/Armor/To Print/Right Gauntlet Shield Clean.stl
113.0 x 117.3 x 134.0
