christian-kramer/Overwatch-Reaper-Costume/Mechanical/Armor/To Print/Right Elbow Cover.stl

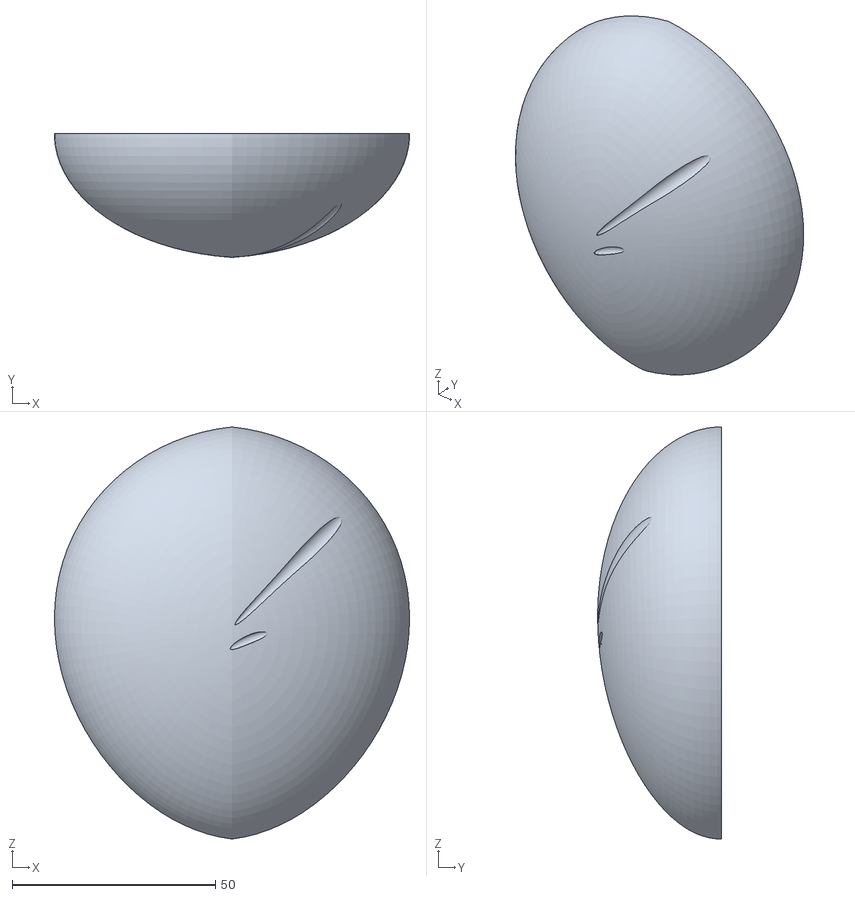
[picture p75: CAD file, 2019-09-04]
Mechanical/Armor/To Print/Right Elbow Cover.stl
87.5 x 30.5 x 101.5
