christian-kramer/Overwatch-Reaper-Costume/Mechanical/Armor/To Print/Right Gauntlet Top.stl

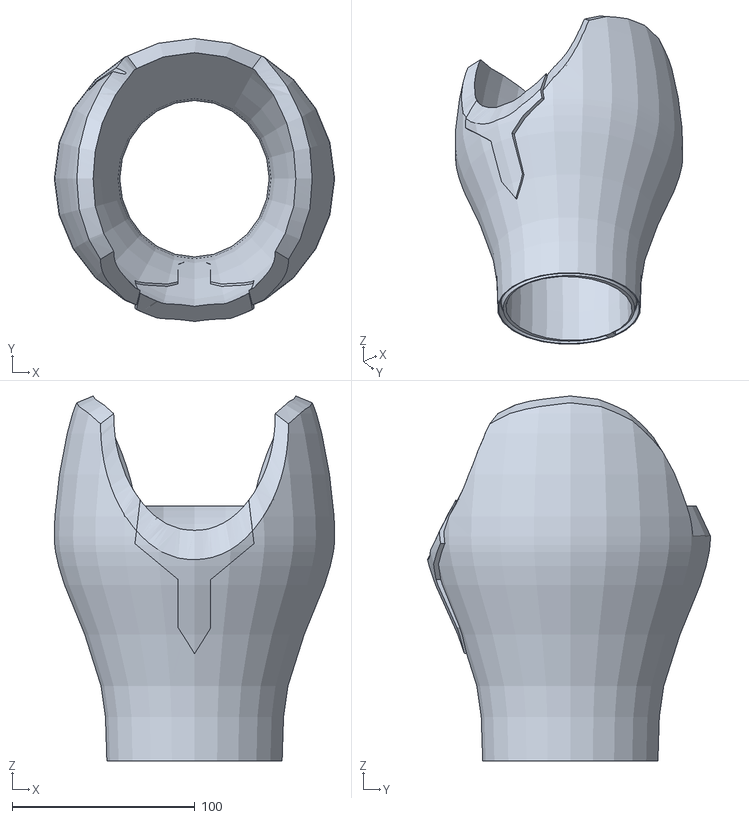
[picture p76: CAD file, 2019-09-04]
Mechanical/Armor/To Print/Right Gauntlet Top.stl
153.6 x 155.0 x 199.9
