christian-kramer/Overwatch-Reaper-Costume/Mechanical/Armor/To Print/Left Gauntlet Shield.stl

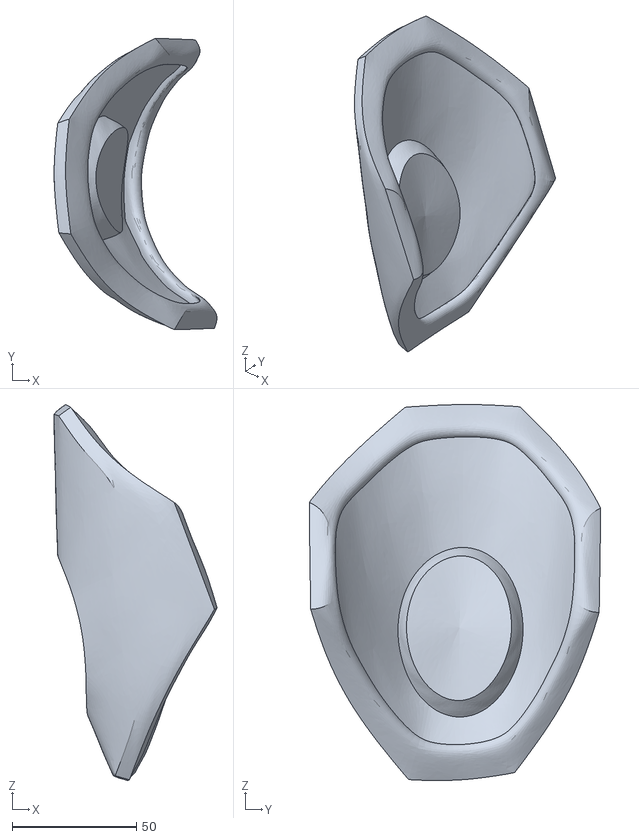
[picture p77: CAD file, 2019-09-04]
Mechanical/Armor/To Print/Left Gauntlet Shield.stl
65.5 x 117.2 x 151.2
