christian-kramer/Overwatch-Reaper-Costume/Mechanical/Armor/To Print/Right Thumb Cover.stl

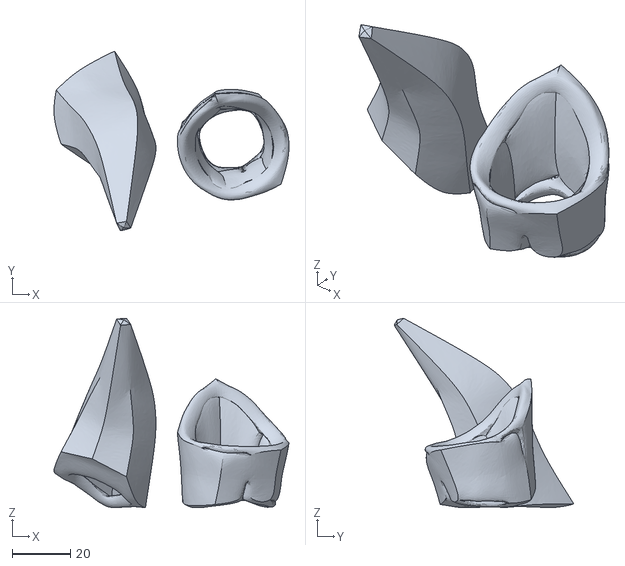
[picture p78: CAD file, 2019-09-03]
Mechanical/Armor/To Print/Right Thumb Cover.stl
80.8 x 61.7 x 65.1
