christian-kramer/Overwatch-Reaper-Costume/Mechanical/Armor/To Print/Right Fingertip Covers.stl

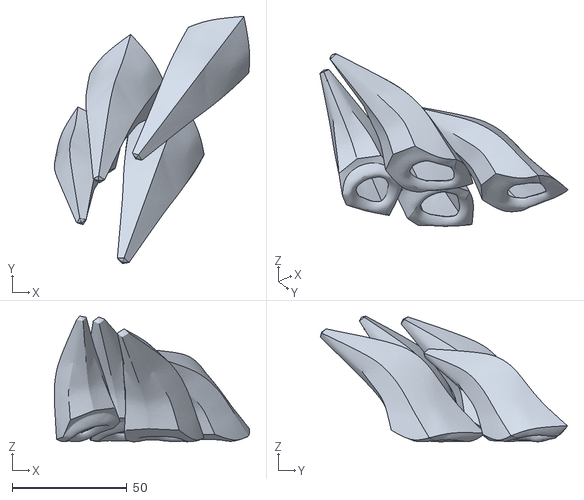
[picture p79: CAD file, 2019-09-03]
Mechanical/Armor/To Print/Right Fingertip Covers.stl
85.0 x 107.5 x 54.7
