christian-kramer/Overwatch-Reaper-Costume/Mechanical/Armor/To Print/Left Fingertip Covers.stl

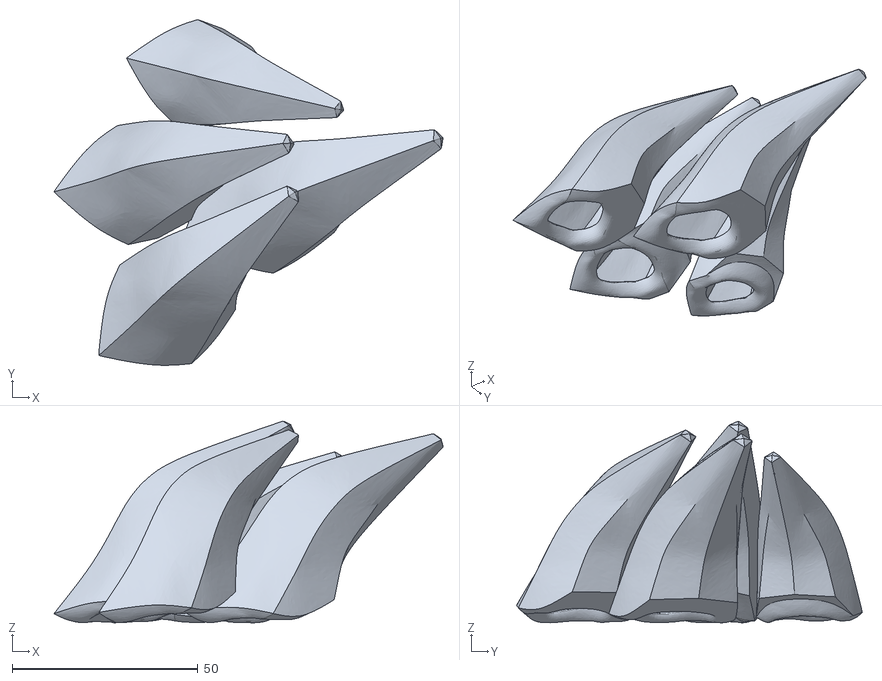
[picture p80: CAD file, 2019-09-03]
Mechanical/Armor/To Print/Left Fingertip Covers.stl
104.7 x 93.1 x 54.3
