christian-kramer/Overwatch-Reaper-Costume/Mechanical/Armor/To Print/Left Thumb Cover.stl

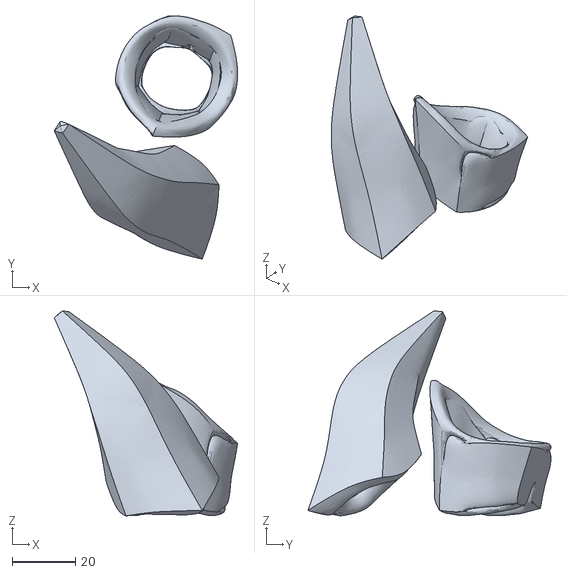
[picture p81: CAD file, 2019-09-02]
Mechanical/Armor/To Print/Left Thumb Cover.stl
57.9 x 76.8 x 64.7
