christian-kramer/Overwatch-Reaper-Costume/Mechanical/Armor/To Print/Left Hand Cover.stl

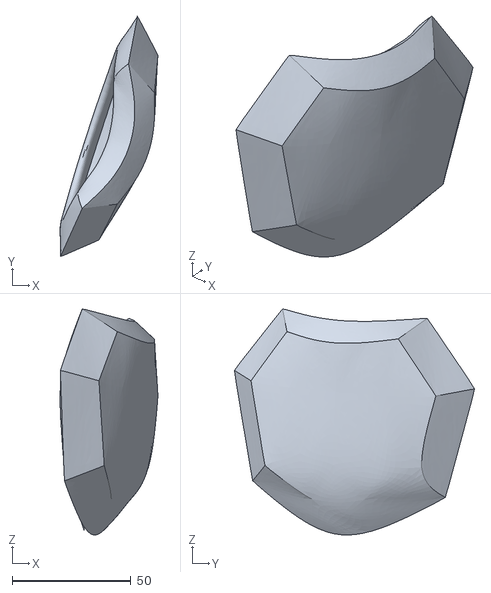
[picture p82: CAD file, 2019-09-02]
Mechanical/Armor/To Print/Left Hand Cover.stl
41.2 x 101.2 x 95.2
