christian-kramer/Overwatch-Reaper-Costume/Mechanical/Armor/To Print/Left Forearm Cover.stl

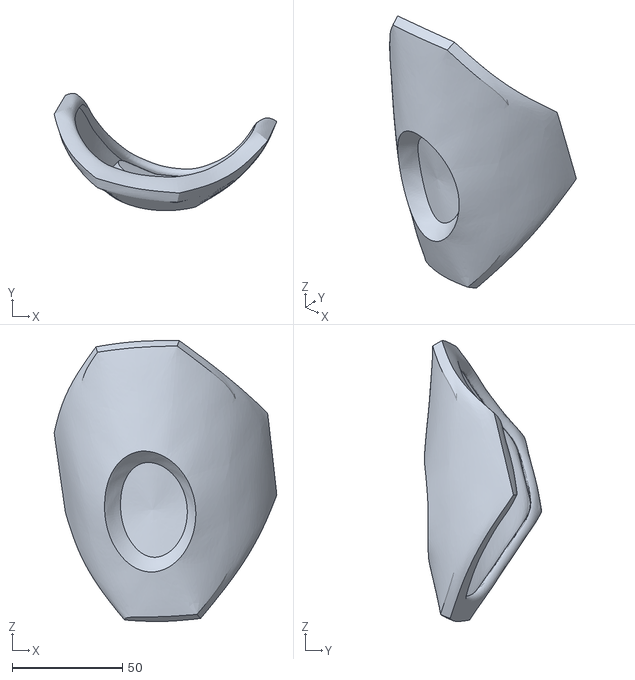
[picture p83: CAD file, 2019-09-02]
Mechanical/Armor/To Print/Left Forearm Cover.stl
100.9 x 53.2 x 127.4
