christian-kramer/Overwatch-Reaper-Costume/Mechanical/Armor/To Print/Calf Cover Pegs.stl

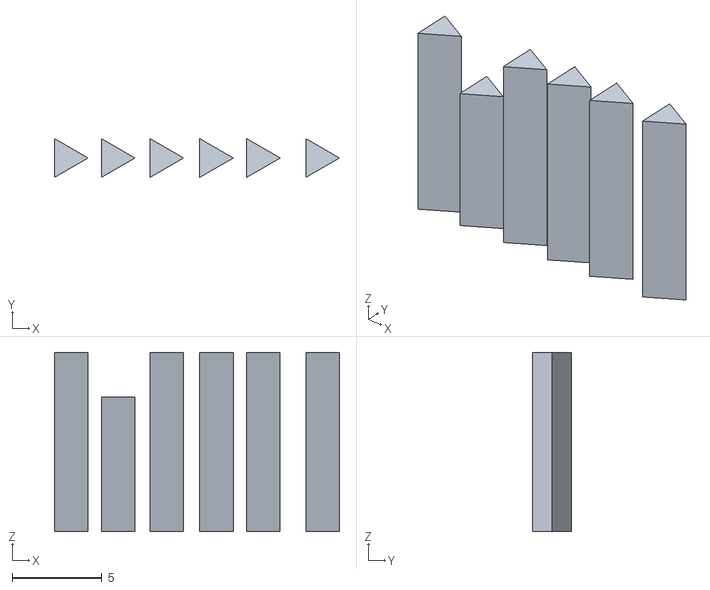
[picture p84: CAD file, 2019-08-23]
Mechanical/Armor/To Print/Calf Cover Pegs.stl
15.9 x 2.17 x 10.0
