christian-kramer/Overwatch-Reaper-Costume/Electrical/Source/PWM Sound Test/Inc/sounddata.h

/*
 * sounddata.h
 *
 *  Created on: May 21, 2019
 *      Author: flyhi
 */

#ifndef SOUNDDATA_H_
#define SOUNDDATA_H_

static const unsigned char sounddata[8880] = {128,
		128, 127, 128, 127, 128, 127, 128, 128, 128, 127, 128, 128, 127, 128, 127, 128, 127, 128, 128, 128,
		127, 128, 127, 128, 128, 128, 127, 128, 127, 128, 128, 127, 128, 127, 128, 127, 128, 128, 127, 128,
		127, 128, 128, 127, 128, 127, 128, 128, 128, 128, 128, 128, 127, 128, 127, 128, 127, 128, 127, 128,
		127, 127, 127, 127, 127, 127, 127, 127, 127, 127, 127, 128, 127, 128, 128, 128, 128, 128, 128, 128,
		128, 128, 128, 128, 128, 128, 128, 127, 127, 127, 127, 127, 127, 127, 127, 127, 127, 127, 127, 127,
		127, 127, 127, 127, 127, 127, 127, 127, 128, 128, 128, 128, 128, 128, 128, 128, 128, 128, 128, 128,
		128, 128, 127, 127, 127, 127, 127, 127, 127, 127, 127, 127, 127, 127, 127, 127, 128, 128, 128, 128,
		128, 128, 128, 128, 128, 128, 128, 128, 128, 128, 128, 128, 128, 128, 128, 128, 128, 127, 127, 127,
		127, 127, 127, 127, 127, 127, 127, 127, 127, 127, 127, 127, 127, 128, 128, 128, 128, 128, 128, 128,
		128, 128, 128, 128, 128, 128, 127, 127, 127, 127, 127, 127, 127, 127, 127, 127, 127, 127, 128, 128,
		128, 127, 127, 127, 127, 128, 127, 127, 128, 128, 128, 127, 127, 127, 127, 127, 127, 126, 126, 127,
		127, 127, 127, 127, 127, 127, 127, 127, 127, 128, 128, 128, 128, 128, 128, 128, 128, 127, 127, 127,
		127, 127, 127, 127, 127, 128, 128, 128, 128, 128, 128, 128, 128, 128, 129, 129, 129, 129, 129, 129,
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
		135, 134, 133, 133, 133, 133, 134, 134, 135, 135, 135, 137, 139, 140, 142, 144, 145, 147, 147, 149,
		150, 150, 150, 150, 149, 148, 146, 144, 142, 139, 136, 134, 130, 127, 124, 122, 120, 118, 116, 115,
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

#endif /* SOUNDDATA_H_ */
